jadonk/beagleconnect/hw/Freedom_C4/report.txt

Plot file "C:\Users\Dwin\Desktop\0713\4\BeagleConnect Freedom-F_Cu.dxf" created.
Plot file "C:\Users\Dwin\Desktop\0713\4\BeagleConnect Freedom-GND.dxf" created.
Plot file "C:\Users\Dwin\Desktop\0713\4\BeagleConnect Freedom-PWR.dxf" created.
Plot file "C:\Users\Dwin\Desktop\0713\4\BeagleConnect Freedom-B_Cu.dxf" created.
Plot file "C:\Users\Dwin\Desktop\0713\4\BeagleConnect Freedom-F_Paste.dxf" created.
Plot file "C:\Users\Dwin\Desktop\0713\4\BeagleConnect Freedom-B_Paste.dxf" created.
Plot file "C:\Users\Dwin\Desktop\0713\4\BeagleConnect Freedom-F_SilkS.dxf" created.
Plot file "C:\Users\Dwin\Desktop\0713\4\BeagleConnect Freedom-B_SilkS.dxf" created.
Plot file "C:\Users\Dwin\Desktop\0713\4\BeagleConnect Freedom-F_Mask.dxf" created.
Plot file "C:\Users\Dwin\Desktop\0713\4\BeagleConnect Freedom-B_Mask.dxf" created.
Plot file "C:\Users\Dwin\Desktop\0713\4\BeagleConnect Freedom-Edge_Cuts.dxf" created.
Plot file "C:\Users\Dwin\Desktop\0713\4\BeagleConnect Freedom-F_Fab.dxf" created.
Plot file "C:\Users\Dwin\Desktop\0713\5\BeagleConnect Freedom-F_Cu.gtl" created.
Plot file "C:\Users\Dwin\Desktop\0713\5\BeagleConnect Freedom-GND.g2" created.
Plot file "C:\Users\Dwin\Desktop\0713\5\BeagleConnect Freedom-PWR.g3" created.
Plot file "C:\Users\Dwin\Desktop\0713\5\BeagleConnect Freedom-B_Cu.gbl" created.
Plot file "C:\Users\Dwin\Desktop\0713\5\BeagleConnect Freedom-F_Paste.gtp" created.
Plot file "C:\Users\Dwin\Desktop\0713\5\BeagleConnect Freedom-B_Paste.gbp" created.
Plot file "C:\Users\Dwin\Desktop\0713\5\BeagleConnect Freedom-F_SilkS.gto" created.
Plot file "C:\Users\Dwin\Desktop\0713\5\BeagleConnect Freedom-B_SilkS.gbo" created.
Plot file "C:\Users\Dwin\Desktop\0713\5\BeagleConnect Freedom-F_Mask.gts" created.
Plot file "C:\Users\Dwin\Desktop\0713\5\BeagleConnect Freedom-B_Mask.gbs" created.
Plot file "C:\Users\Dwin\Desktop\0713\5\BeagleConnect Freedom-Edge_Cuts.gm1" created.
创建 Gerber 工作文件 C:\Users\Dwin\Desktop\0713\5\BeagleConnect Freedom-job.gbrjob
