jadonk/beagleconnect/case/Industrial design/base-pcb1.png

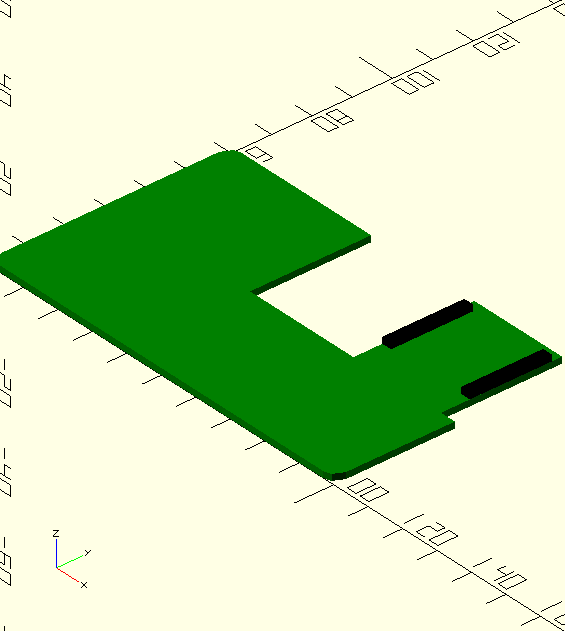
case/Industrial design/base-pcb1.png
