jadonk/beagleconnect/case/Industrial design/BeagleConnect_ID_4.png

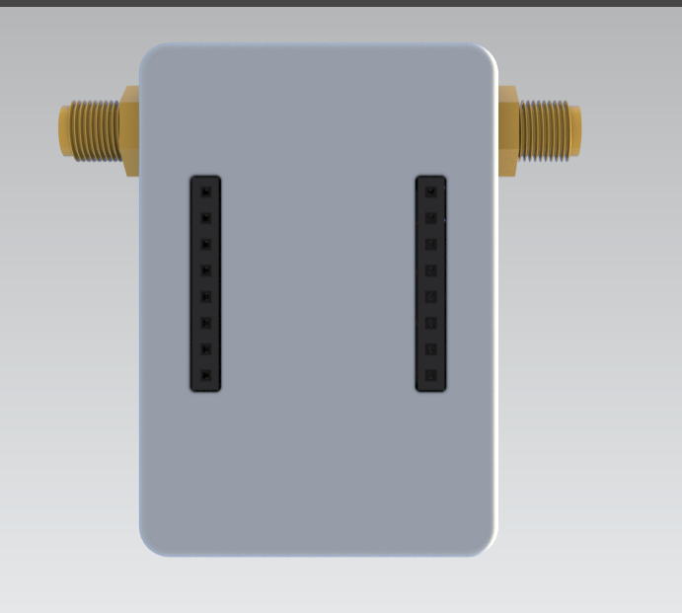
case/Industrial design/BeagleConnect_ID_4.png
