jadonk/beagleconnect/case/Industrial design/BeagleConnect_ID_5.png

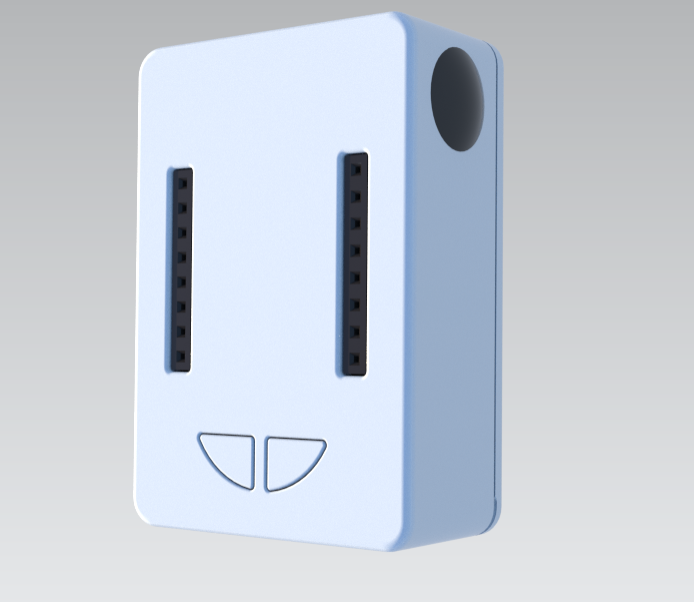
case/Industrial design/BeagleConnect_ID_5.png
