jadonk/beagleconnect/case/Industrial design/BeagleConnect_ID_6.png

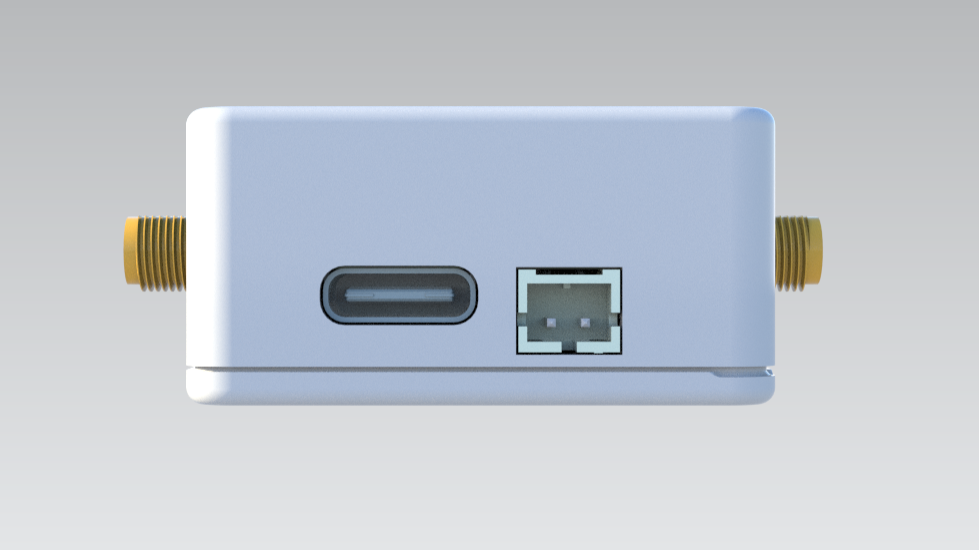
case/Industrial design/BeagleConnect_ID_6.png
