jadonk/beagleconnect/case/Industrial design/BeagleConnnect_ID_8.png

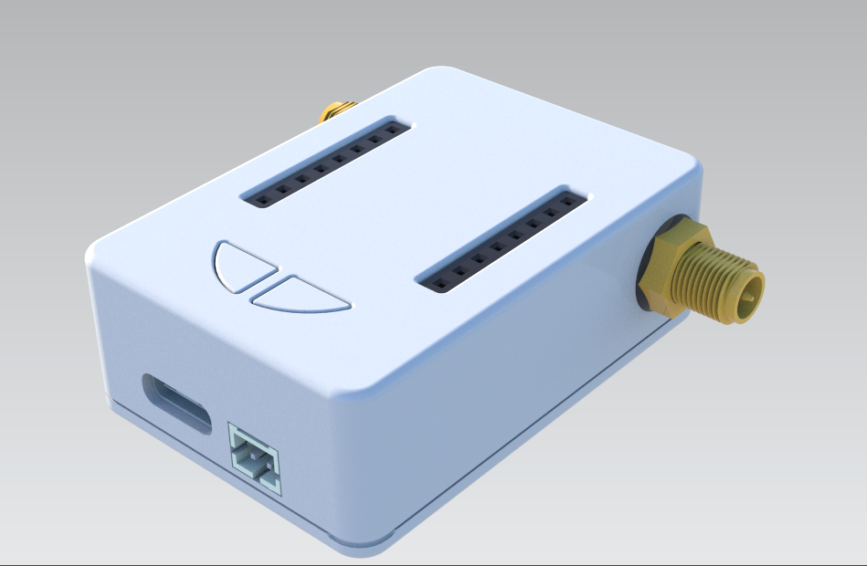
case/Industrial design/BeagleConnnect_ID_8.png
