jadonk/beagleconnect/case/Industrial design/ID-20210603-jk.png

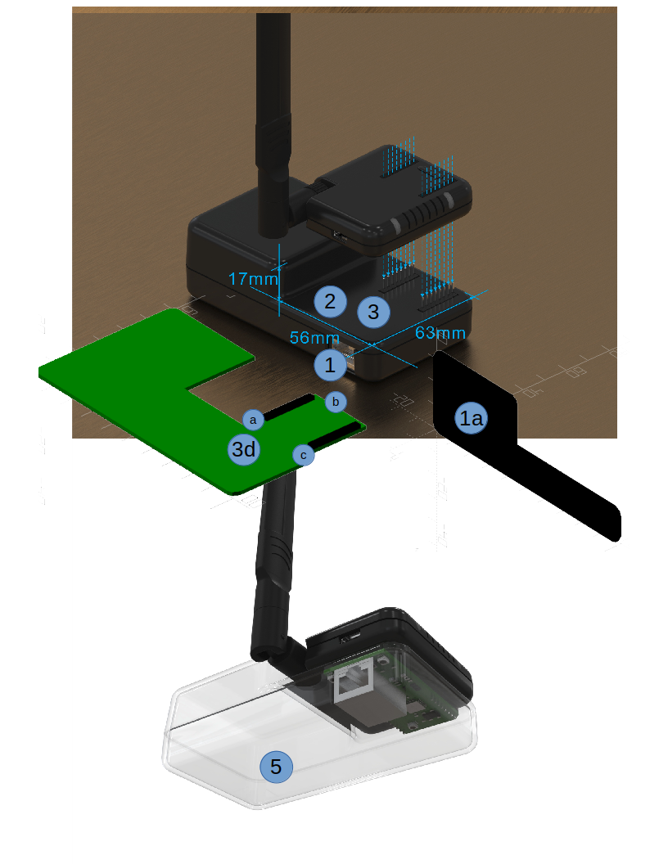
case/Industrial design/ID-20210603-jk.png
