jadonk/beagleconnect/case/mechanical design/case-silkscreen.png

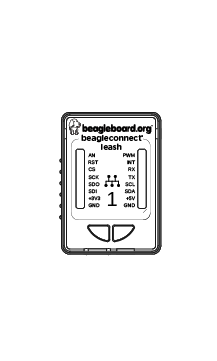
case/mechanical design/case-silkscreen.png
