jadonk/beagleconnect/docs/MVIMG_20200410_095337.jpg

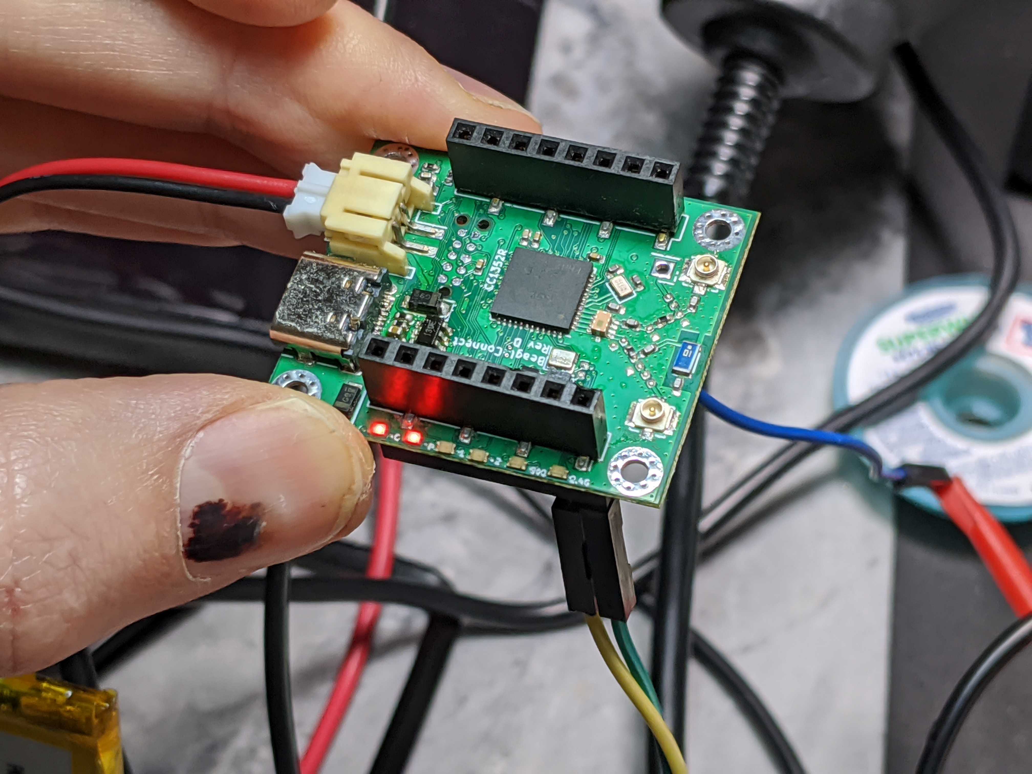
docs/MVIMG_20200410_095337.jpg
