jadonk/beagleconnect/docs/SoftwareProp.PNG

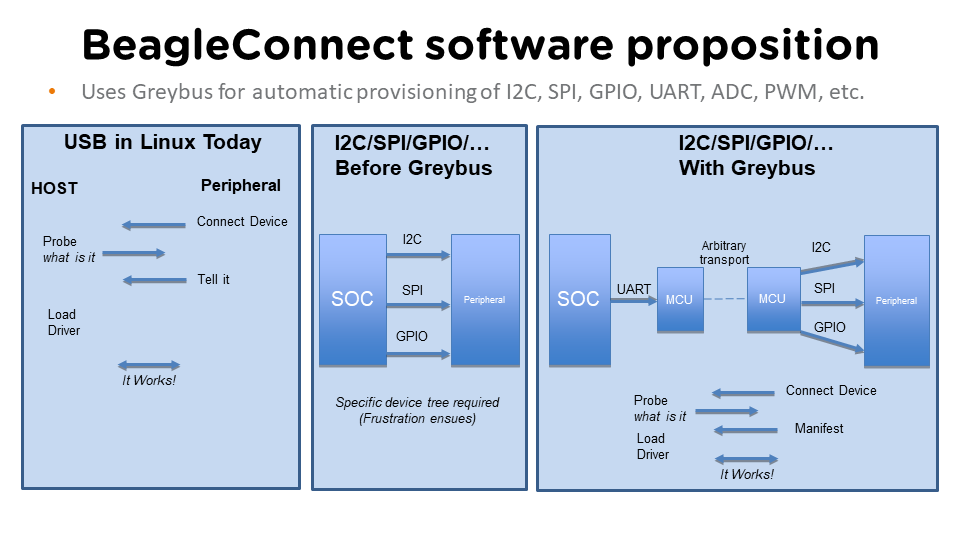
docs/SoftwareProp.PNG
