jadonk/beagleconnect/graphics/bb-code-server-closeup.png

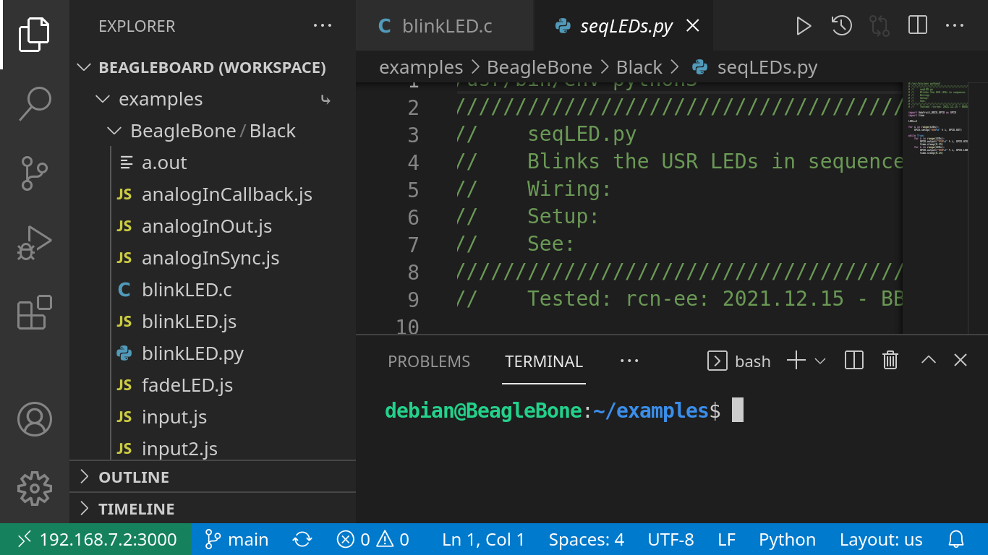
graphics/bb-code-server-closeup.png
