jadonk/beagleconnect/graphics/bb-code-server.png

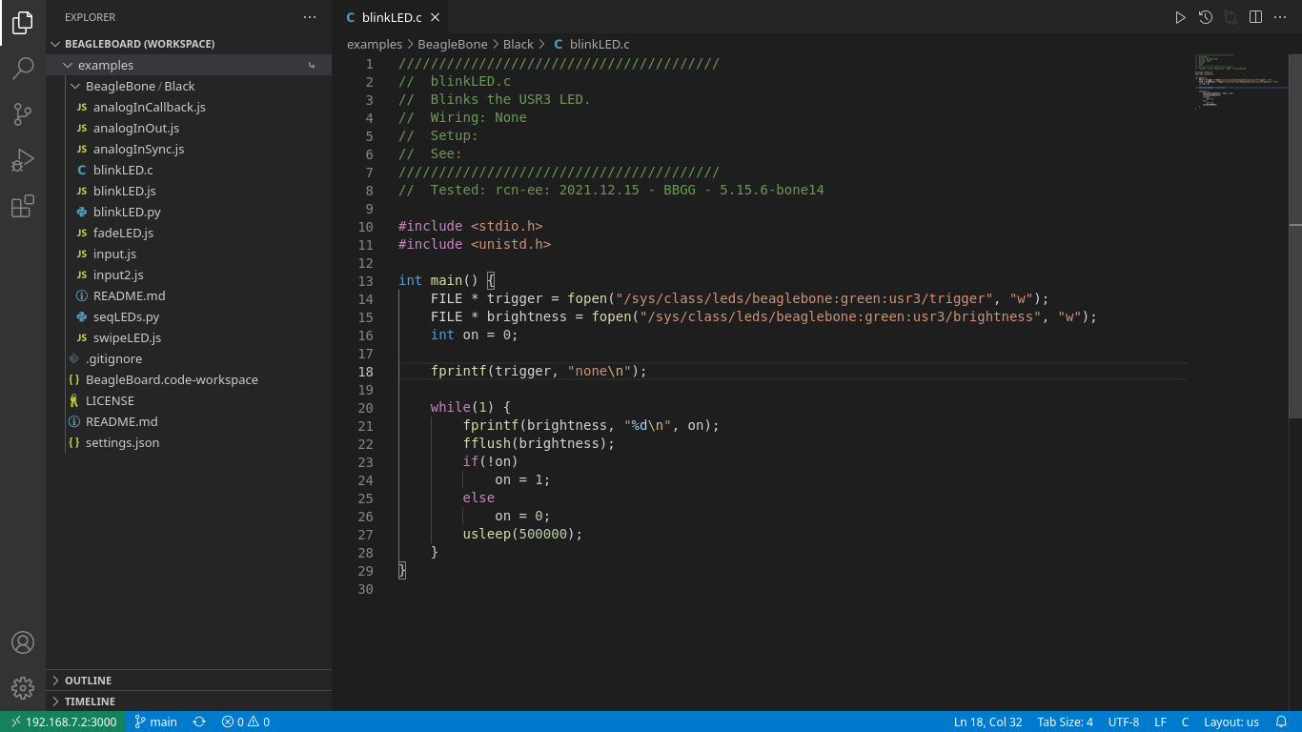
graphics/bb-code-server.png
