jadonk/beagleconnect/graphics/BeagleConnect-Freedom-C5-Boards-Presentation.png

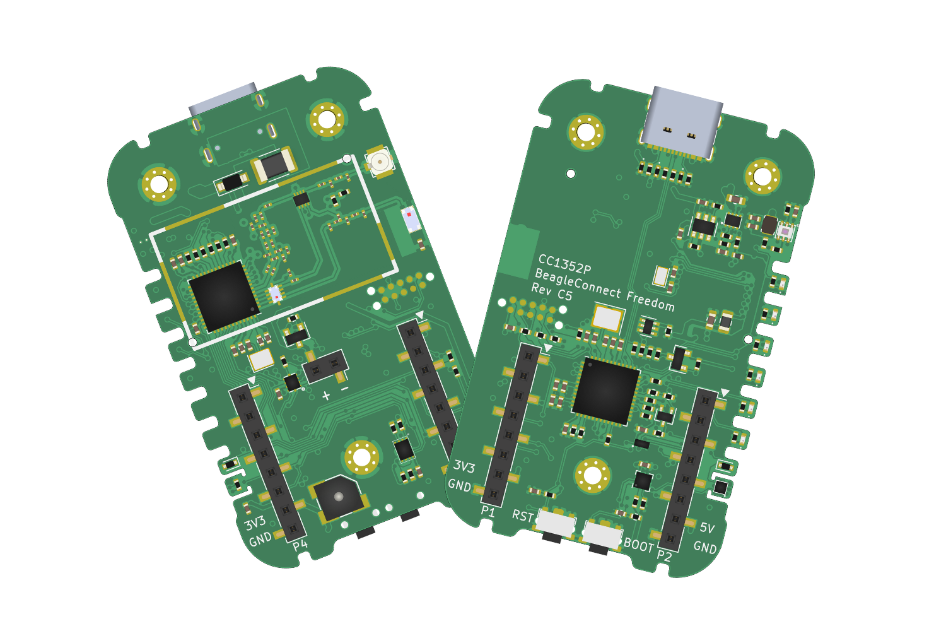
graphics/BeagleConnect-Freedom-C5-Boards-Presentation.png
