jadonk/beagleconnect/graphics/BeagleConnectFreedom-Back-Annotated.png

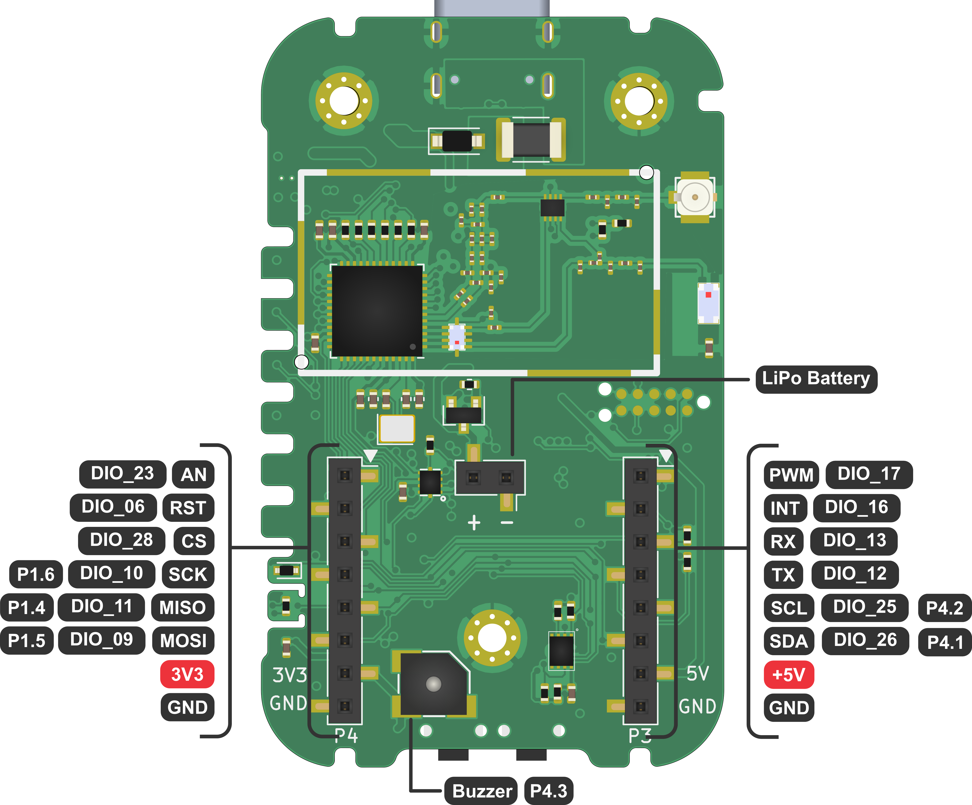
graphics/BeagleConnectFreedom-Back-Annotated.png
