jadonk/beagleconnect/graphics/BeagleConnectFreedom-Back.png

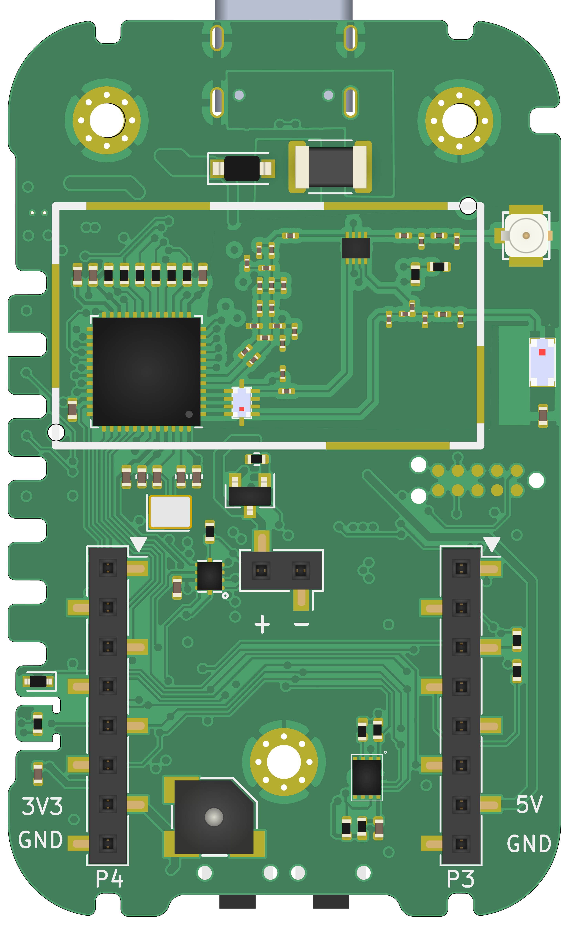
graphics/BeagleConnectFreedom-Back.png
