jadonk/beagleconnect/graphics/BeagleConnectFreedom-Front-Annotated.png

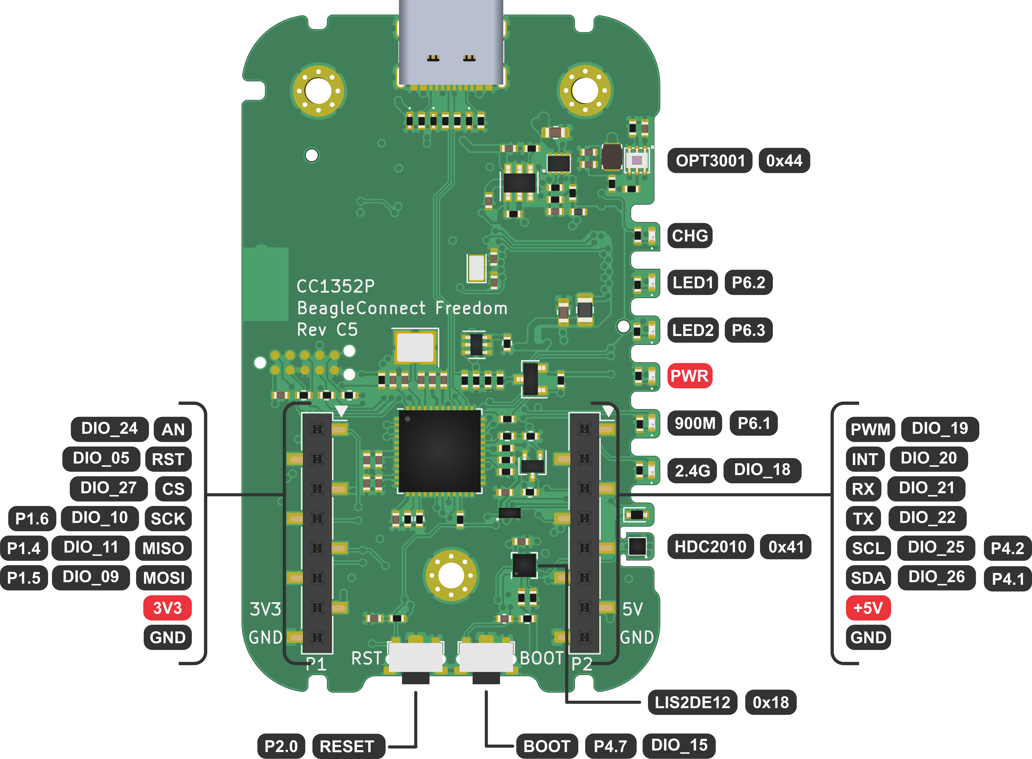
graphics/BeagleConnectFreedom-Front-Annotated.png
