jadonk/beagleconnect/graphics/BeagleConnectFreedom-Front.png

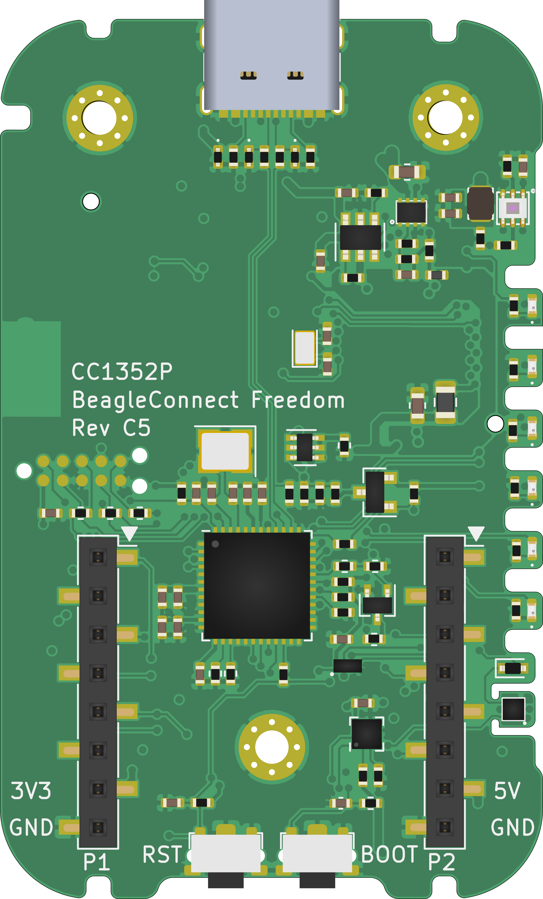
graphics/BeagleConnectFreedom-Front.png
