jadonk/beagleconnect/hw/Freedom_C4/mech/YPA0006ABAB_TEX.step

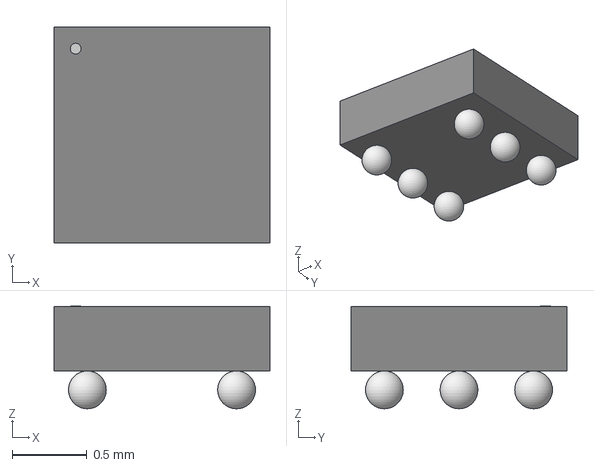
[picture p70: CAD file, 2020-08-28]
hw/Freedom_C4/mech/YPA0006ABAB_TEX.step
1.45 x 1.45 x 0.688 mm
