jadonk/beagleconnect/hw/Freedom_C4/mech/LGA-12_STM-M.step

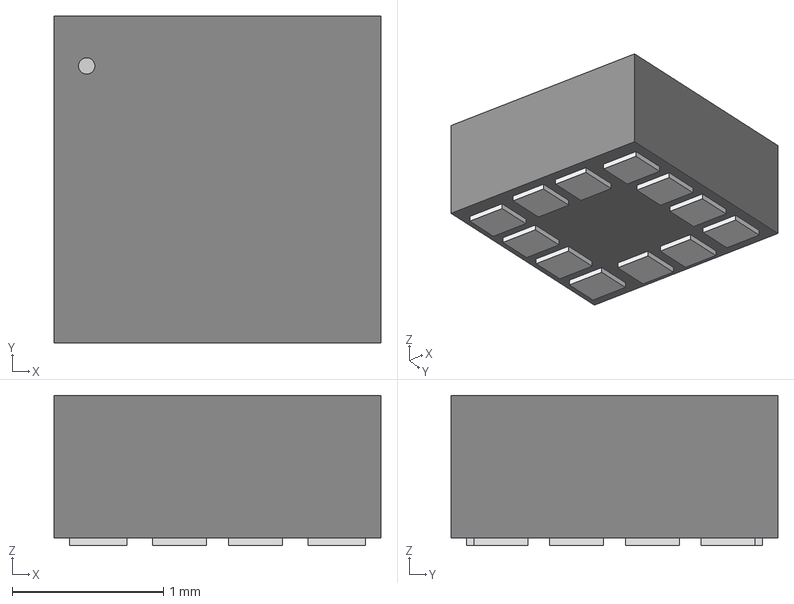
[picture p71: CAD file, 2020-08-28]
hw/Freedom_C4/mech/LGA-12_STM-M.step
2.16 x 2.16 x 0.993 mm
