jadonk/beagleconnect/hw/Freedom_C4/mech/USB Type C Port (SMD Type).STEP

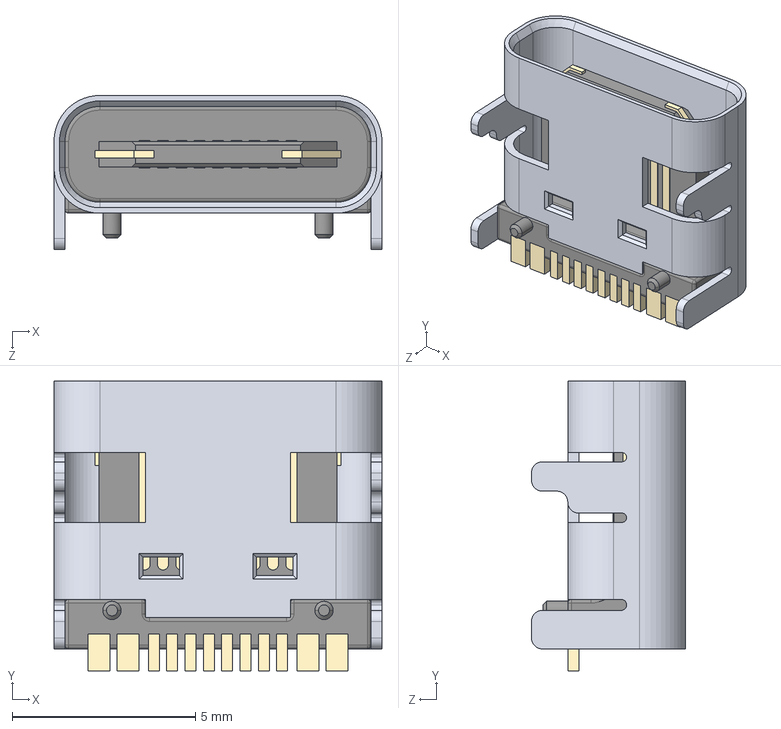
[picture p72: CAD file, 2020-08-28]
hw/Freedom_C4/mech/USB Type C Port (SMD Type).STEP
8.94 x 7.90 x 4.20 mm
