jadonk/beagleconnect/hw/Freedom_C4/mech/a_1jb_3d_model_file.stp

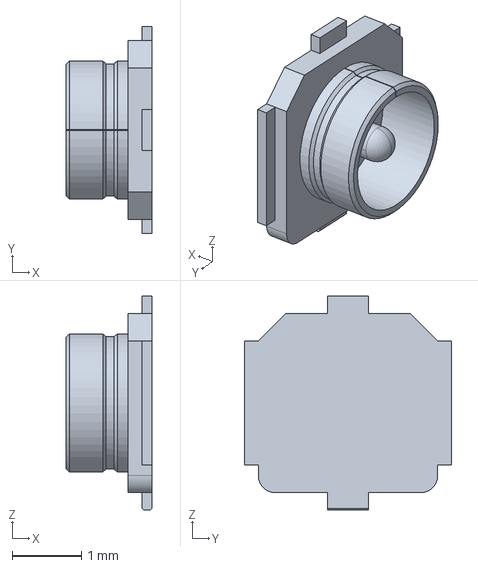
[picture p73: CAD file, 2019-07-19]
hw/Freedom_C4/mech/a_1jb_3d_model_file.stp
1.25 x 3.00 x 3.10 mm
