jadonk/beagleconnect/hw/Freedom_C4/mech/EVQP7-JA-01P.STEP

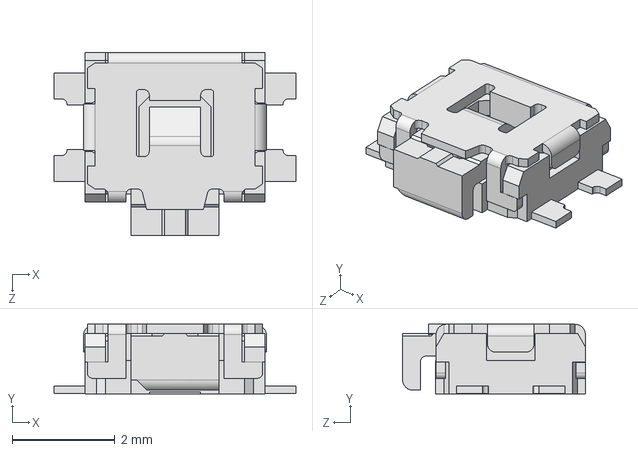
[picture p74: CAD file, 2019-07-19]
hw/Freedom_C4/mech/EVQP7-JA-01P.STEP
4.70 x 1.35 x 3.55 mm
