jadonk/beagleconnect/hw/Freedom_C4/mech/AAA Battery.STEP

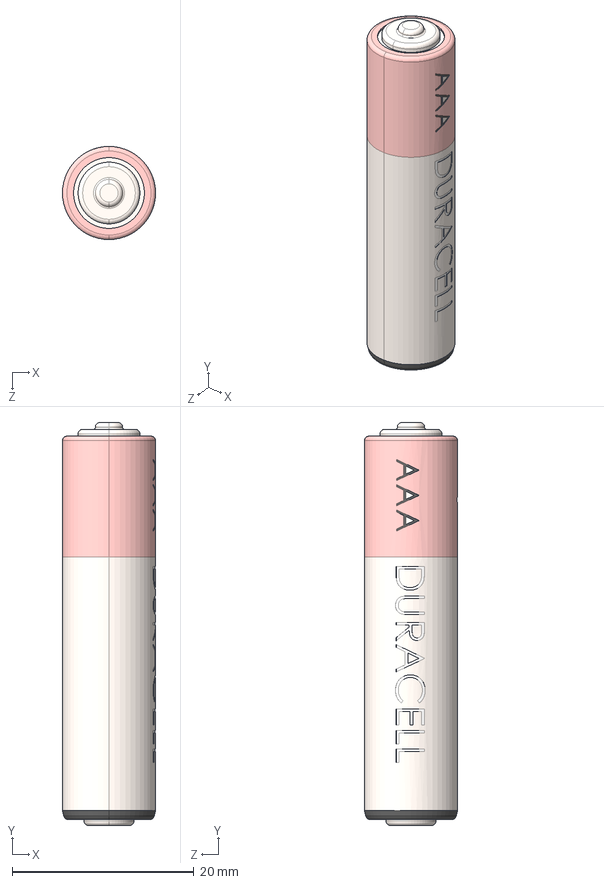
[picture p75: CAD file, 2019-07-19]
hw/Freedom_C4/mech/AAA Battery.STEP
10.2 x 44.4 x 10.2 mm
