jadonk/beagleconnect/hw/Freedom_C4/mech/Leash_061319.step

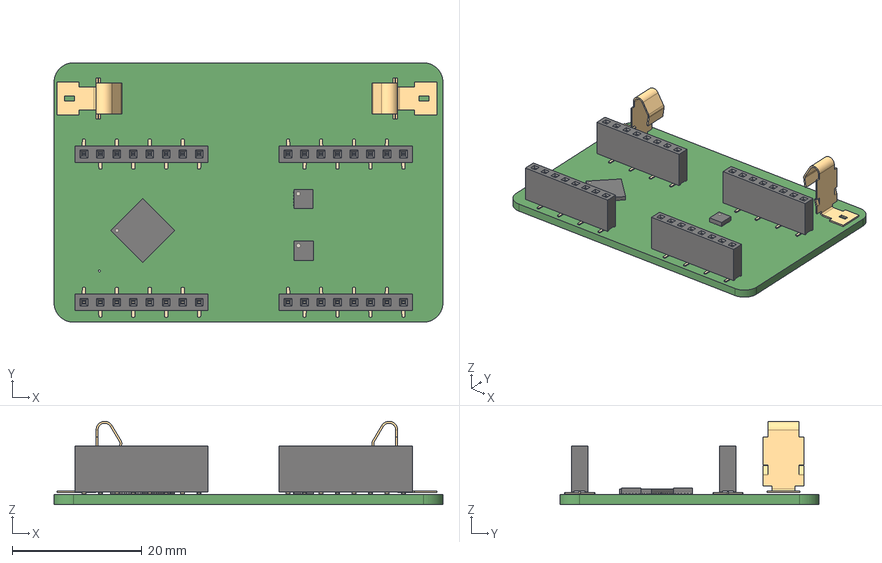
[picture p76: CAD file, 2019-06-13]
hw/Freedom_C4/mech/Leash_061319.step
60.0 x 40.0 x 12.9 mm
