jadonk/beagleconnect/docs/ProvStep1.PNG

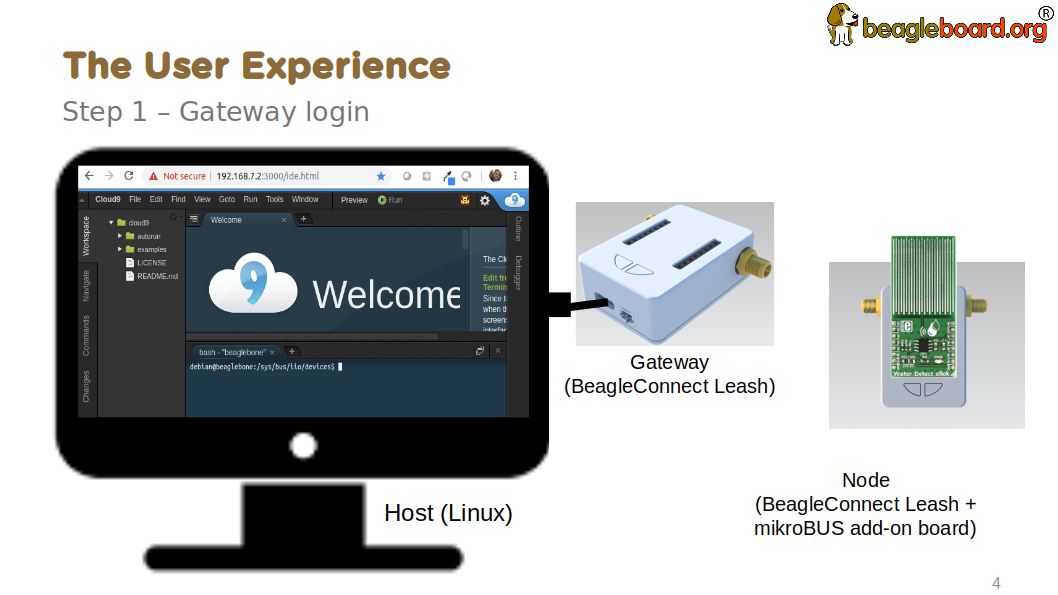
docs/ProvStep1.PNG
