jadonk/beagleconnect/hw/Leash/BeagleConnect.pdf

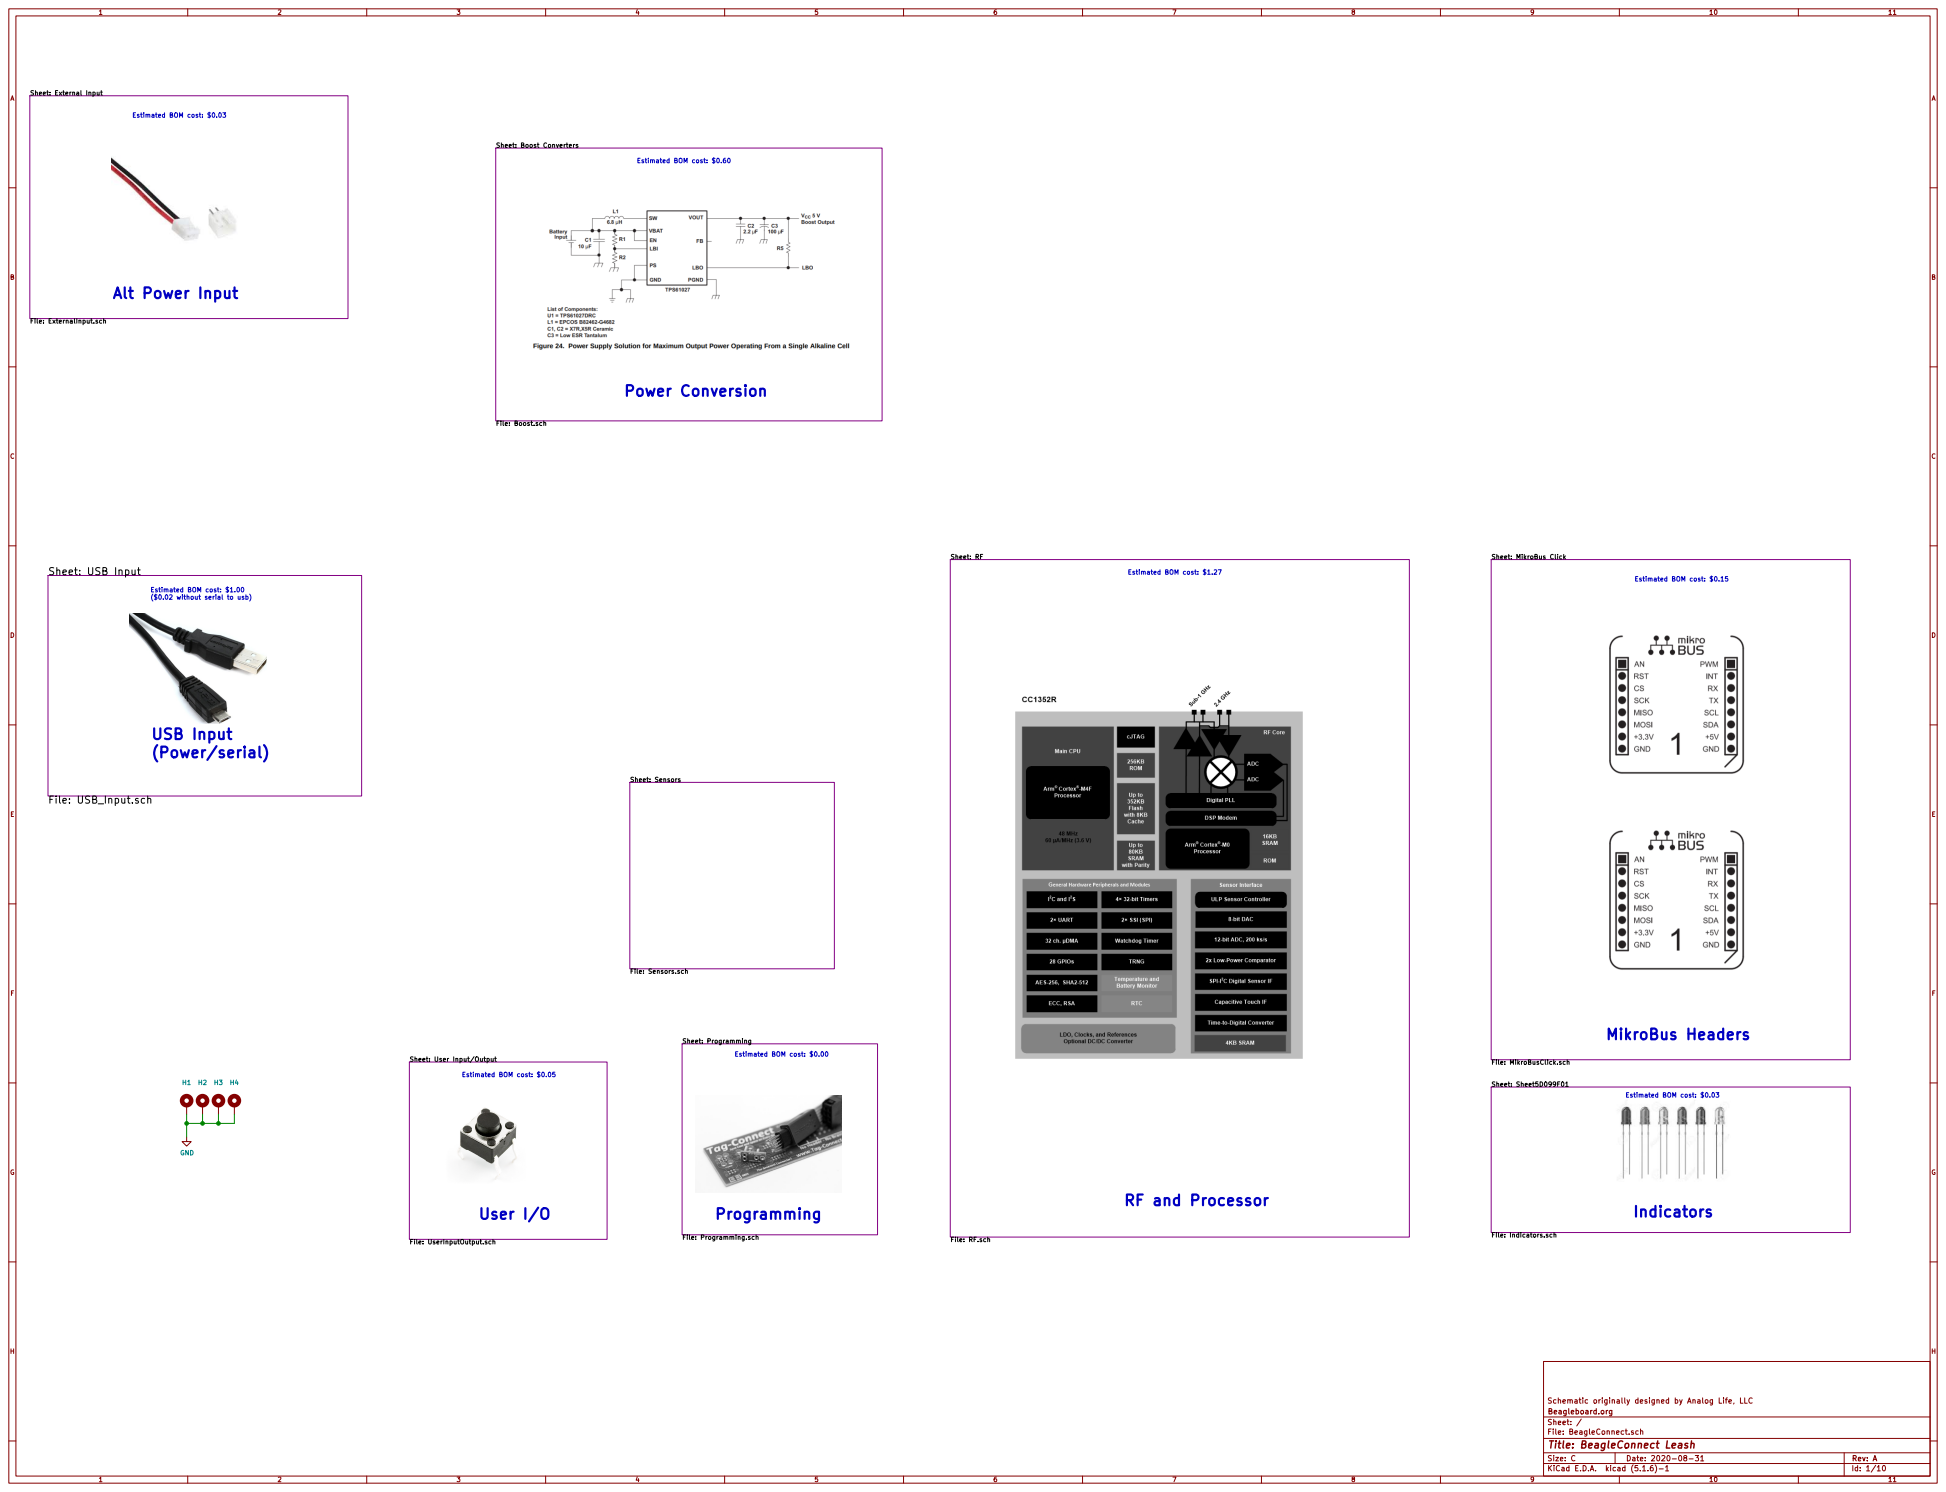
[picture p92: page 1]

Sheet: Boost Converters File: Boost.sch Sheet: USB Input

Estimated BOM cost: $1.00
($0.02 without serial to usb)

Sheet: Sensors File: Sensors.sch Sheet: User Input/Output

Sheet: Sheet5D099F01 File: Indicators.sch GND

Schematic originally designed by Analog Life, LLC
File: BeagleConnect.sch Sheet: / Beagleboard.org

Id: 1/10 Title: BeagleConnect Leash

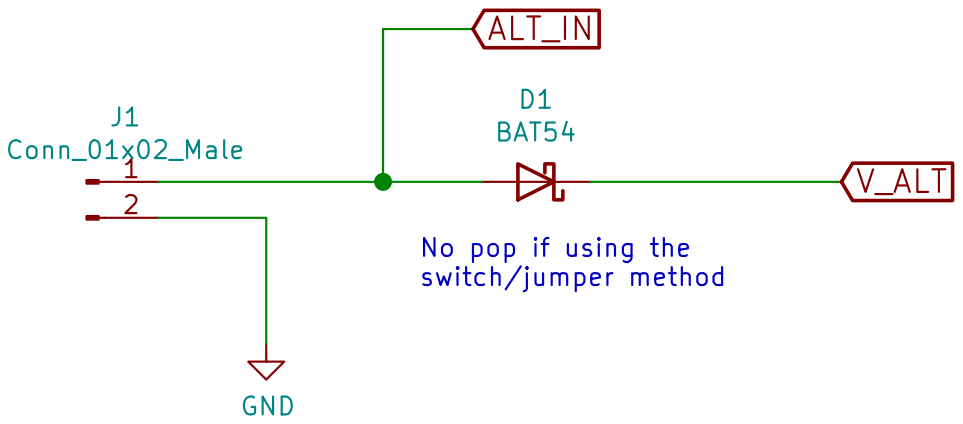
[picture p93: page 2]

No pop if using the
switch/jumper method

Schematic originally designed by Analog Life, LLC
Beagleboard.org
Sheet: /External Input/
File: ExternalInput.sch
Id: 2/10 Title: BeagleConnect Leash

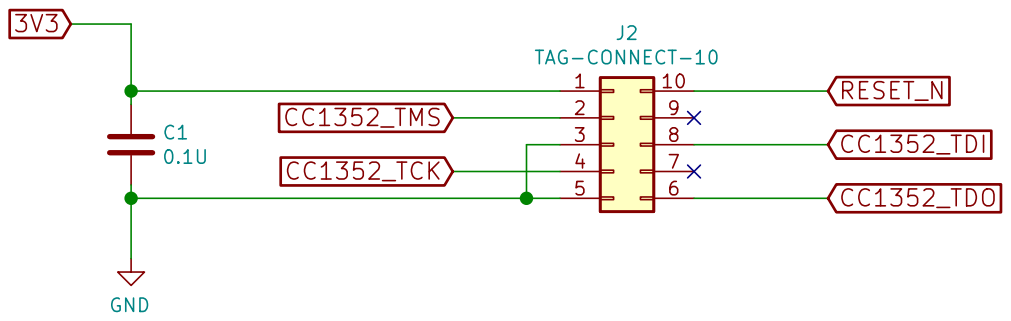
[picture p94: page 3]

Schematic originally designed by Analog Life, LLC
Beagleboard.org
Sheet: /Programming/
File: Programming.sch
Id: 3/10 Title: BeagleConnect Leash


Schematic originally designed by Analog Life, LLC
File: Indicators.sch Sheet: /Sheet5D099F01/ Beagleboard.org

Id: 4/10 Title: BeagleConnect Leash

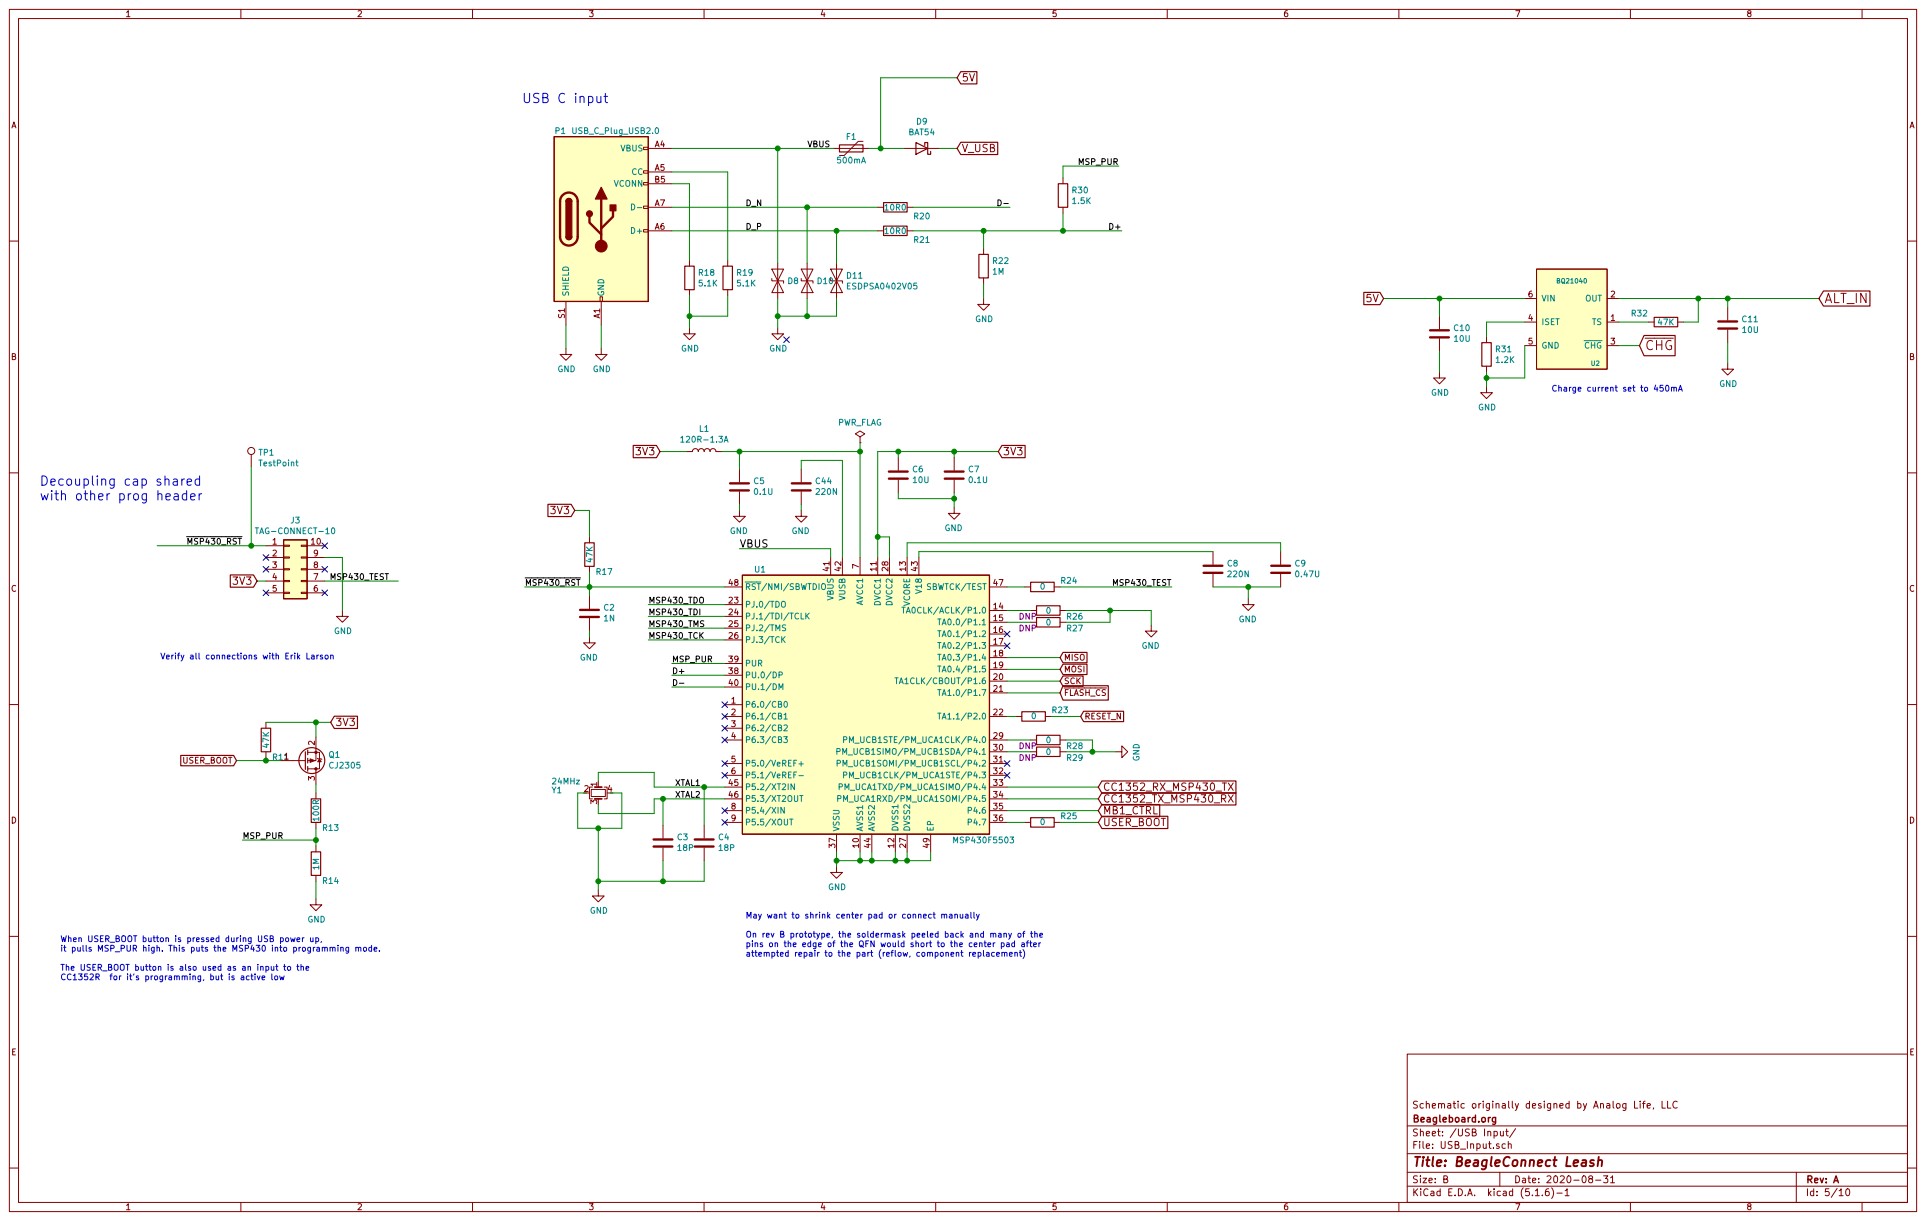
[picture p95: page 5]

Charge current set to 450mA

Decoupling cap shared
with other prog header

Verify all connections with Erik Larson

When USER_BOOT button is pressed during USB power up,
it pulls MSP_PUR high. This puts the MSP430 into programming mode.

On rev B prototype, the soldermask peeled back and many of the
pins on the edge of the QFN would short to the center pad after
attempted repair to the part (reflow, component replacement)

The USER_BOOT button is also used as an input to the
CC1352R for it's programming, but is active low

Schematic originally designed by Analog Life, LLC
Beagleboard.org
Sheet: /USB Input/
File: USB_Input.sch
Id: 5/10 Title: BeagleConnect Leash

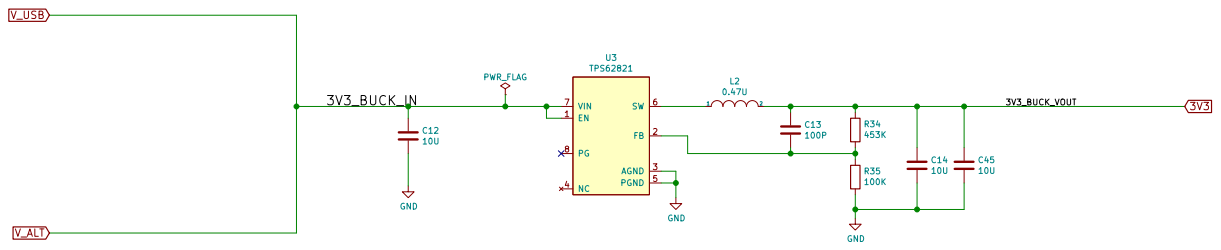
[picture p96: page 6]

Schematic originally designed by Analog Life, LLC
File: Boost.sch Sheet: /Boost Converters/ Beagleboard.org

Id: 6/10 Title: BeagleConnect Leash


Schematic originally designed by Analog Life, LLC
File: MikroBusClick.sch Sheet: /MikroBus Click/ Beagleboard.org

Id: 7/10 Title: BeagleConnect Leash

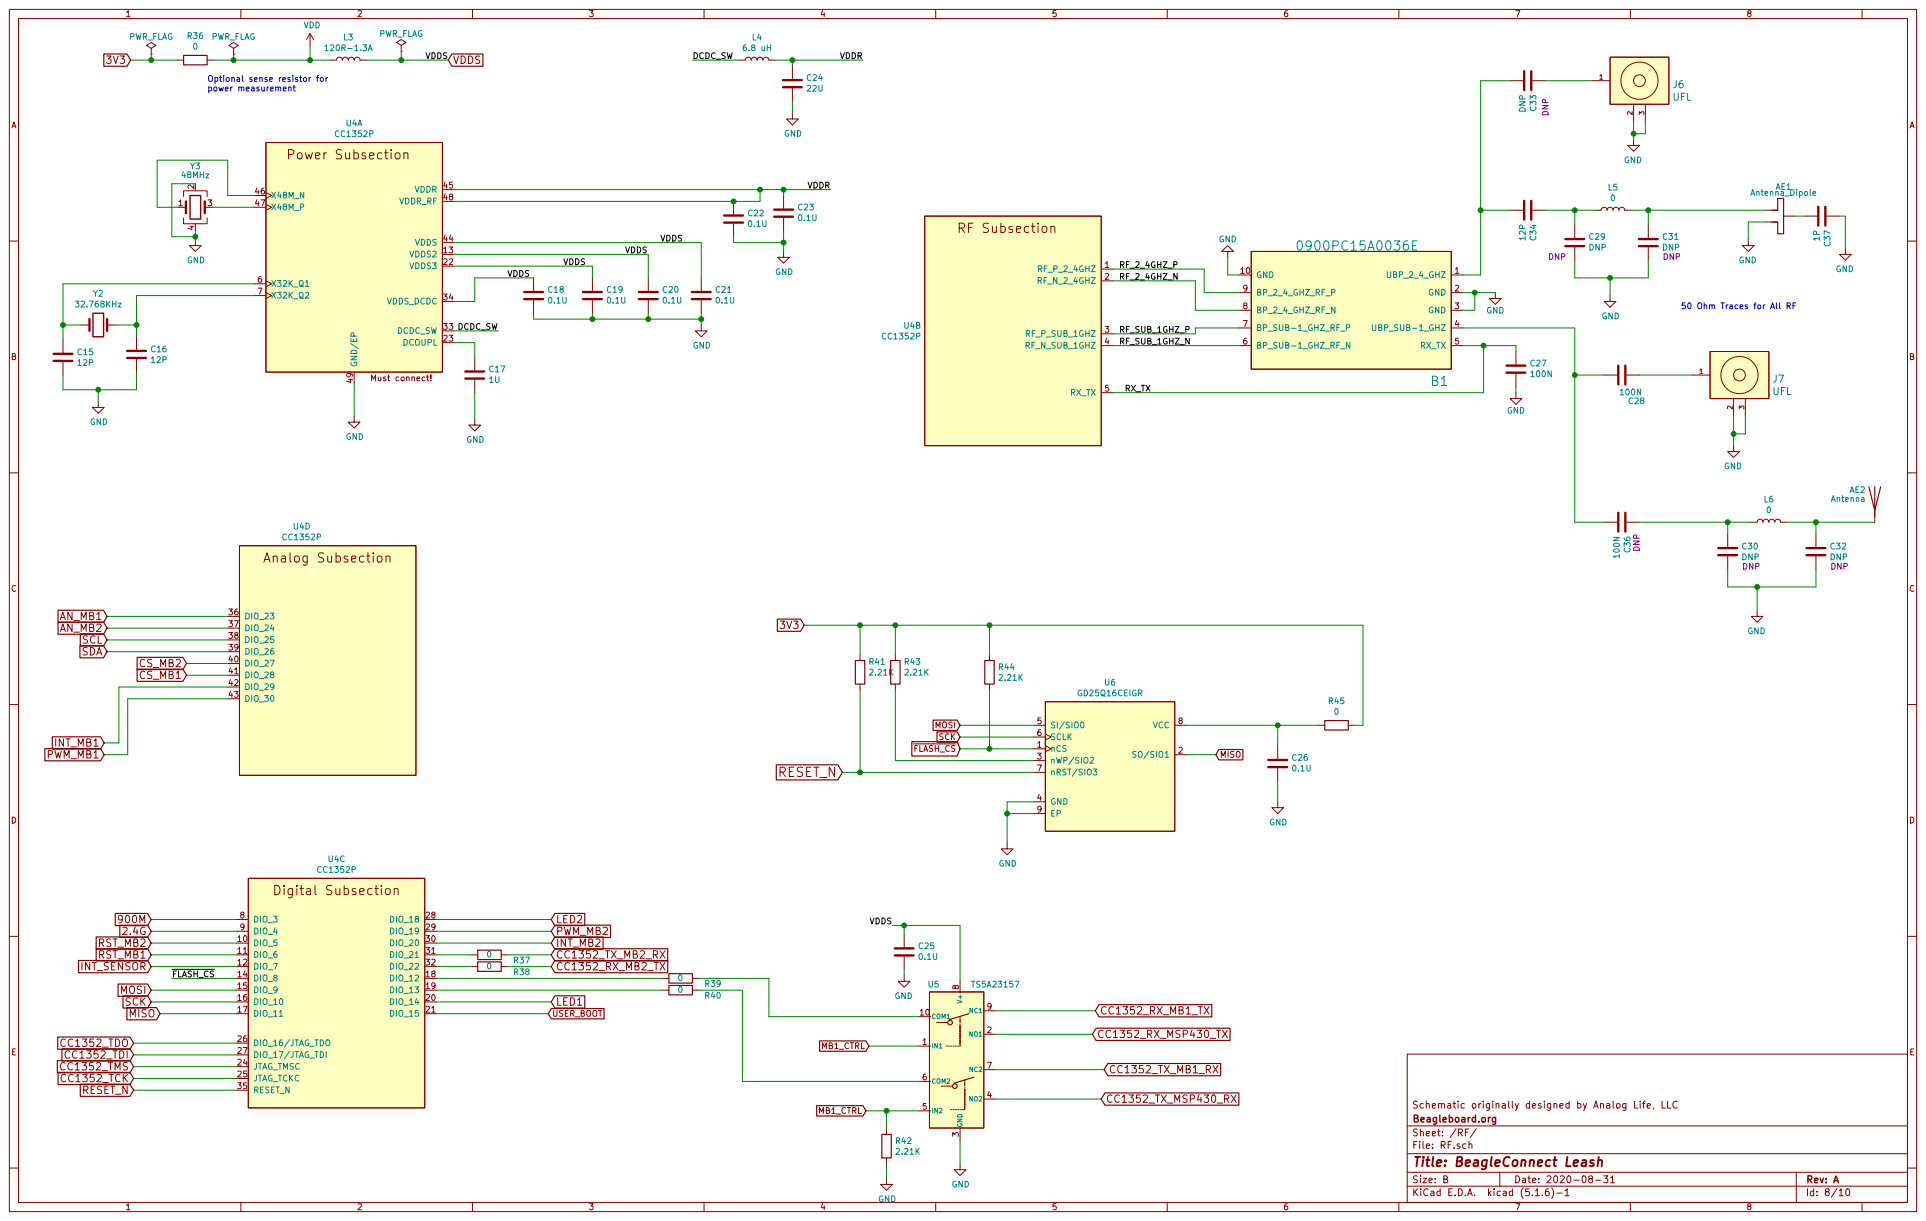
[picture p97: page 8]

50 Ohm Traces for All RF Optional sense resistor for power measurement

Schematic originally designed by Analog Life, LLC
File: RF.sch Sheet: /RF/ Beagleboard.org

Id: 8/10 Title: BeagleConnect Leash

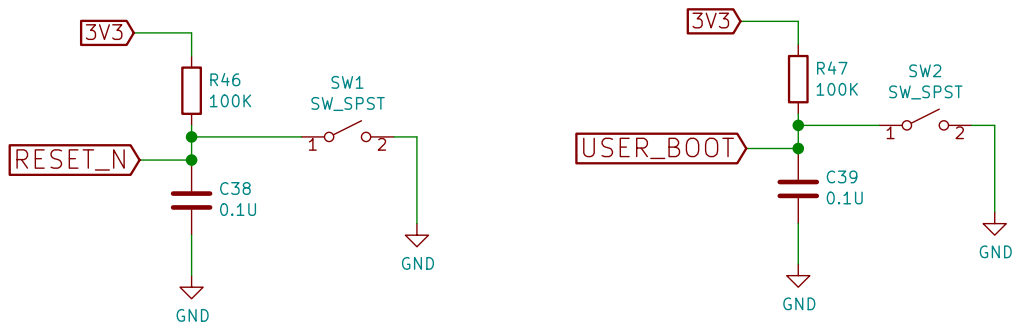
[picture p98: page 9]

Schematic originally designed by Analog Life, LLC
Beagleboard.org
Sheet: /User Input/Output/
File: UserInputOutput.sch
Id: 9/10 Title: BeagleConnect Leash

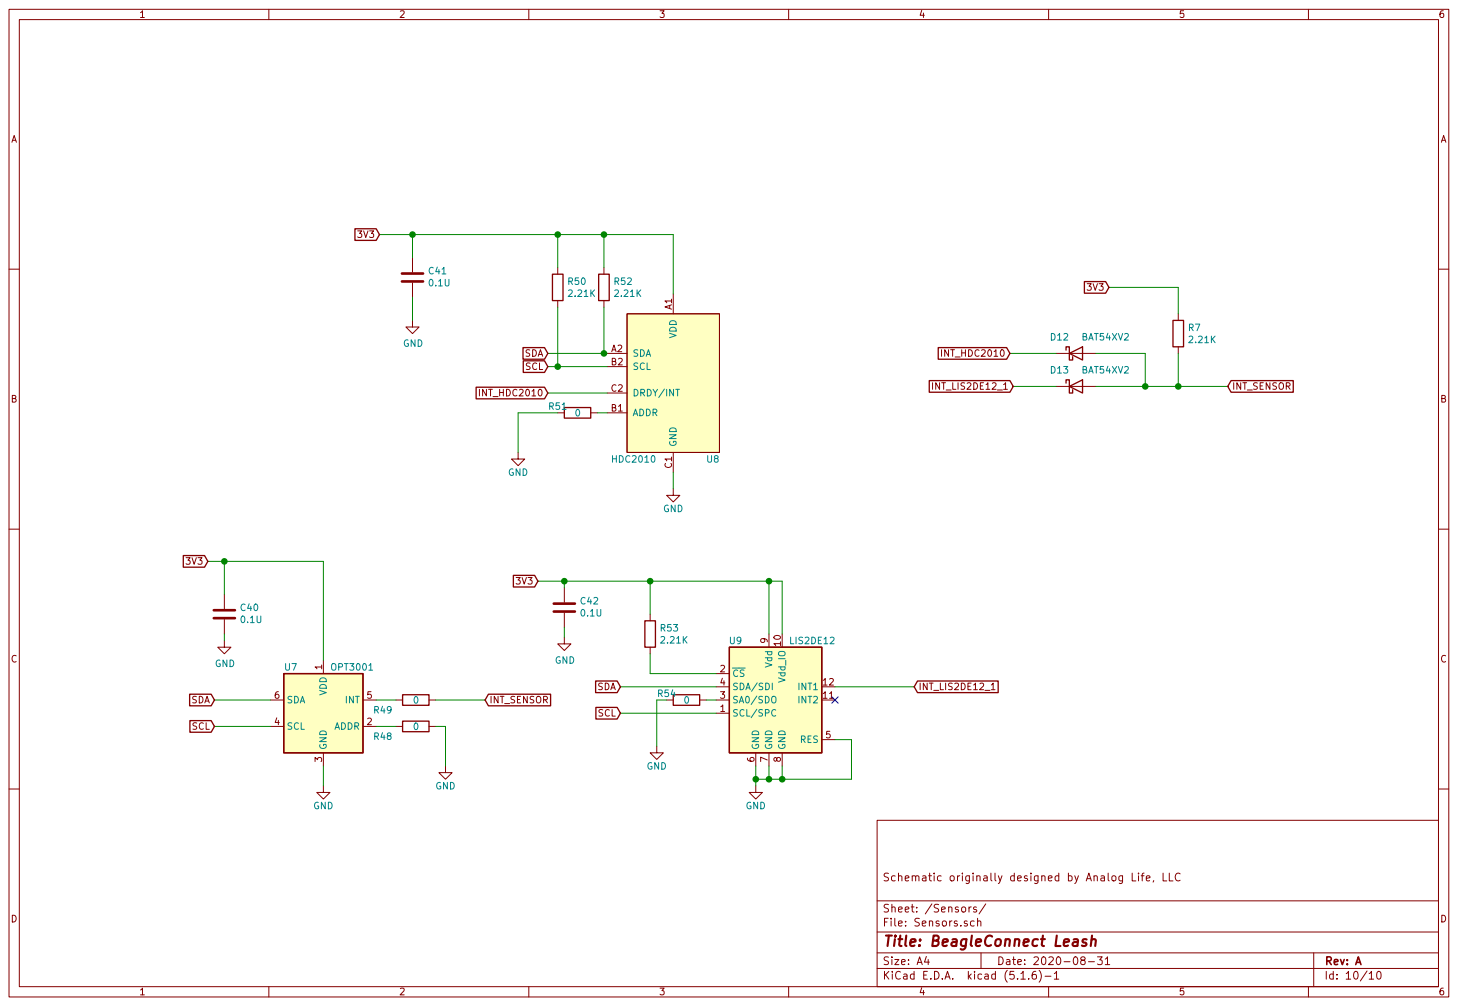
[picture p99: page 10]

File: Sensors.sch Sheet: /Sensors/ Schematic originally designed by Analog Life, LLC

Id: 10/10 Title: BeagleConnect Leash
