jadonk/beagleconnect/hw/Freedom_C4/gerber/0722.pdf

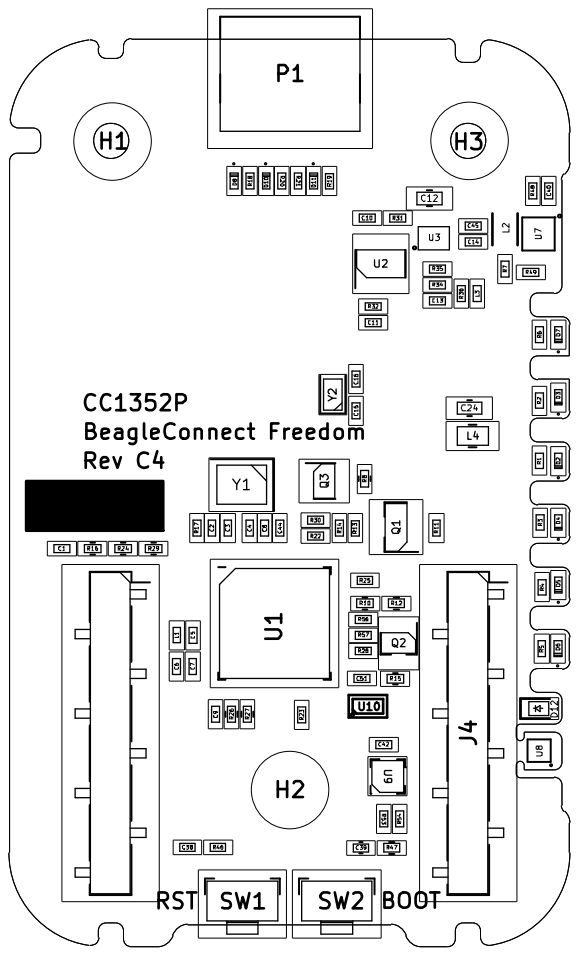
[picture p117: page 1]
