jadonk/beagleconnect/hw/Freedom_C4/mech/TopLayerAntenna.pdf

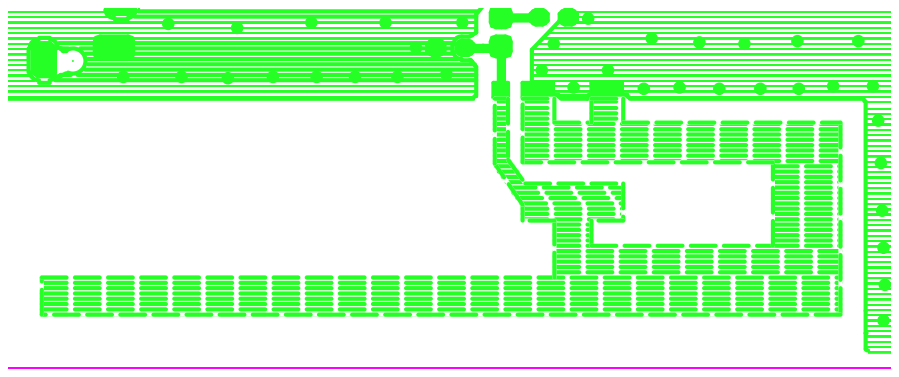
[picture p118: page 1]
