jadonk/beagleconnect/hw/Freedom/BeagleConnect Freedom.pdf

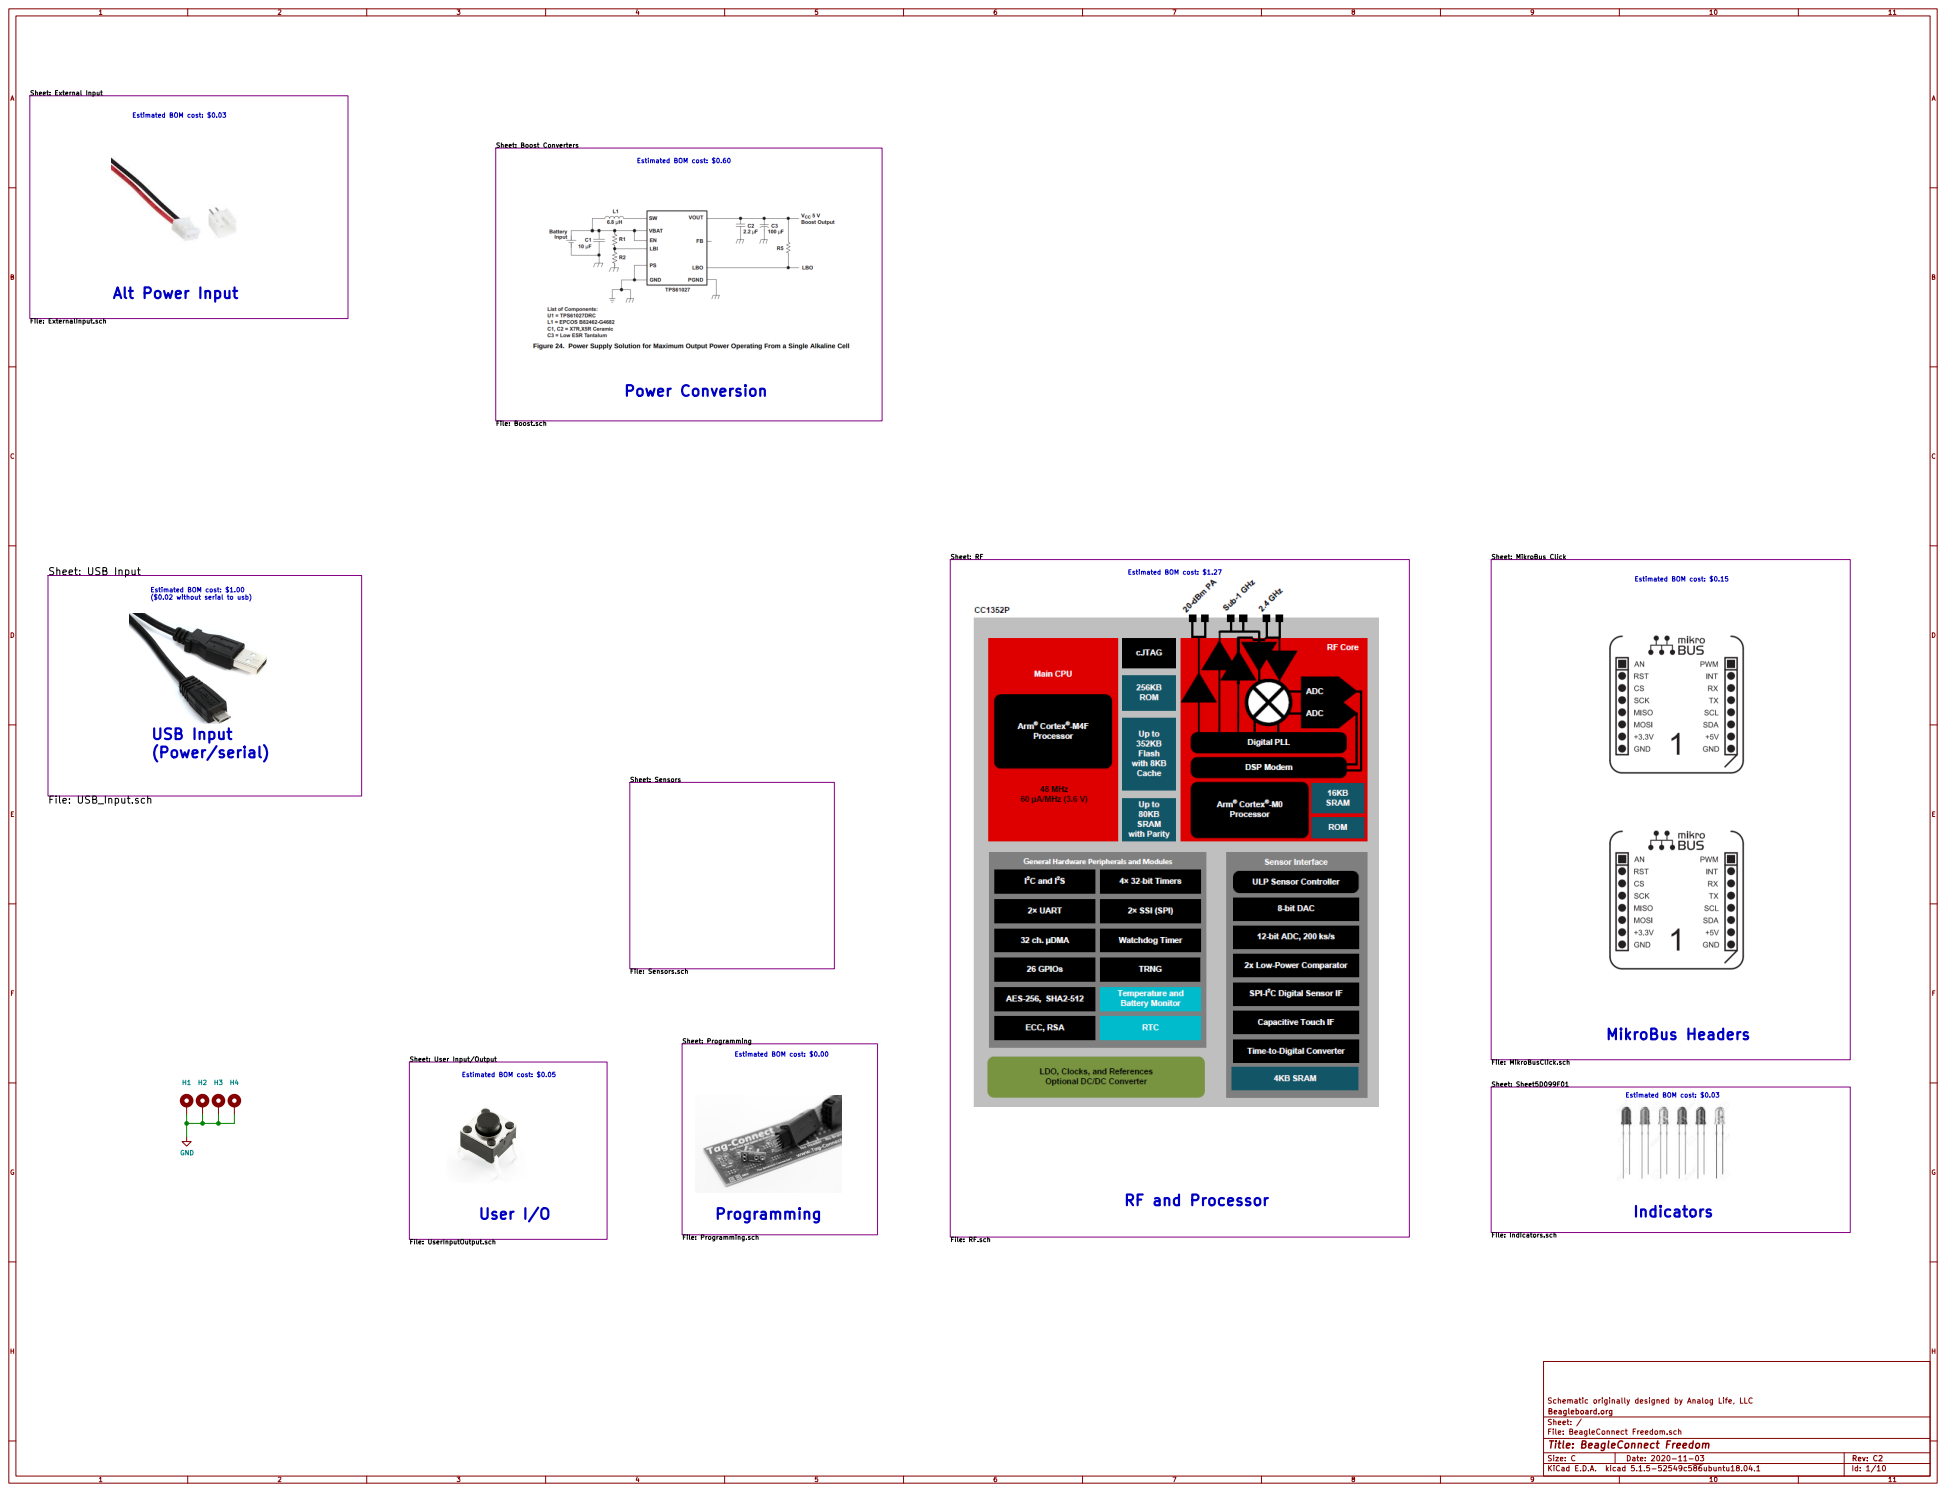
[picture p119: page 1]

Estimated BOM cost: $0.60 Estimated BOM cost: $1.00

Estimated BOM cost: $1.27 USB Input

($0.02 without serial to usb)

Sheet: Sensors File: Sensors.sch Sheet: User Input/Output File: UserInputOutput.sch

Sheet: Programming File: Programming.sch

Sheet: Sheet5D099F01 File: Indicators.sch GND

File: BeagleConnect Freedom.sch Sheet: / Beagleboard.org Schematic originally designed by Analog Life, LLC

Id: 1/10 Title: BeagleConnect Freedom

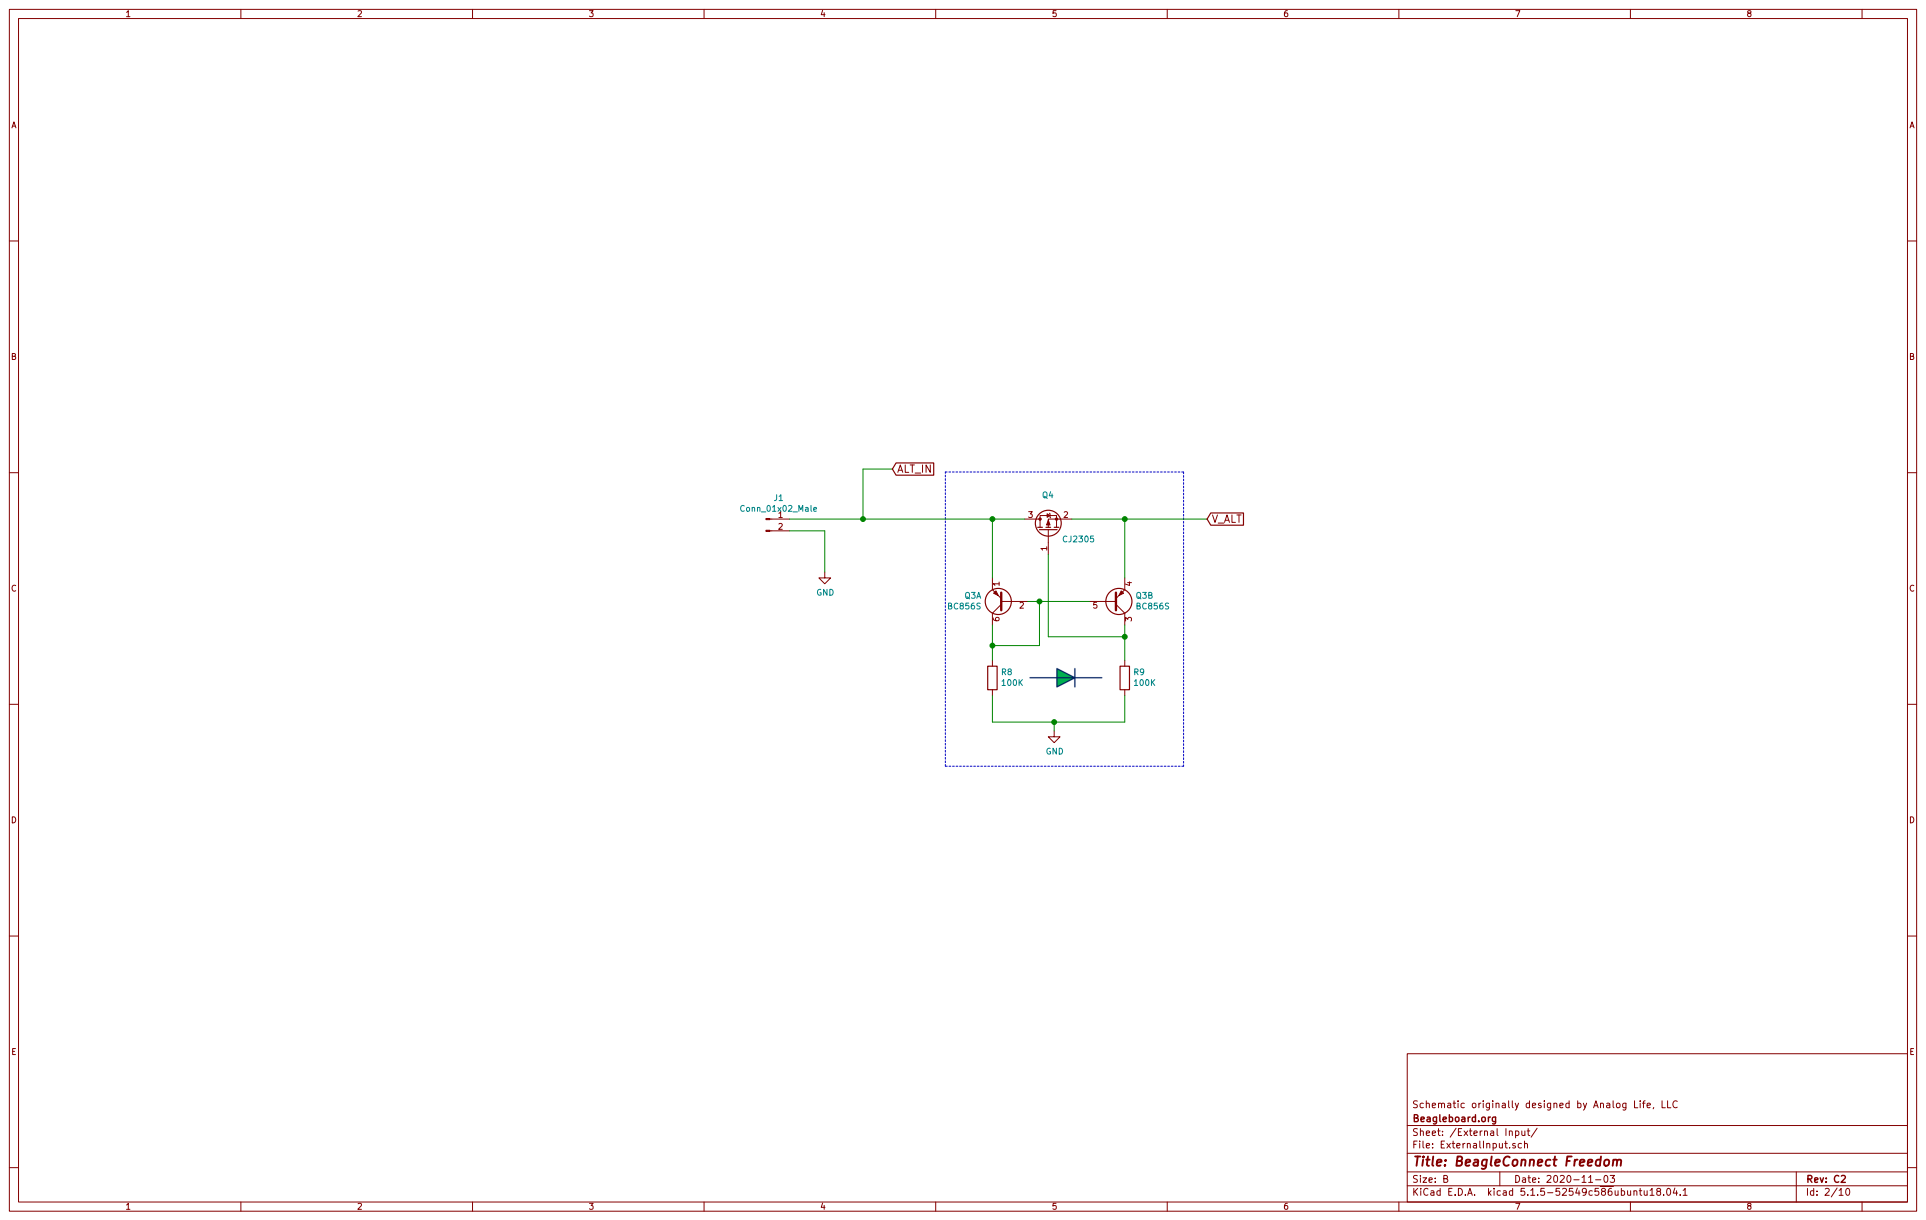
[picture p120: page 2]

File: ExternalInput.sch Sheet: /External Input/ Beagleboard.org Schematic originally designed by Analog Life, LLC

Id: 2/10 Title: BeagleConnect Freedom

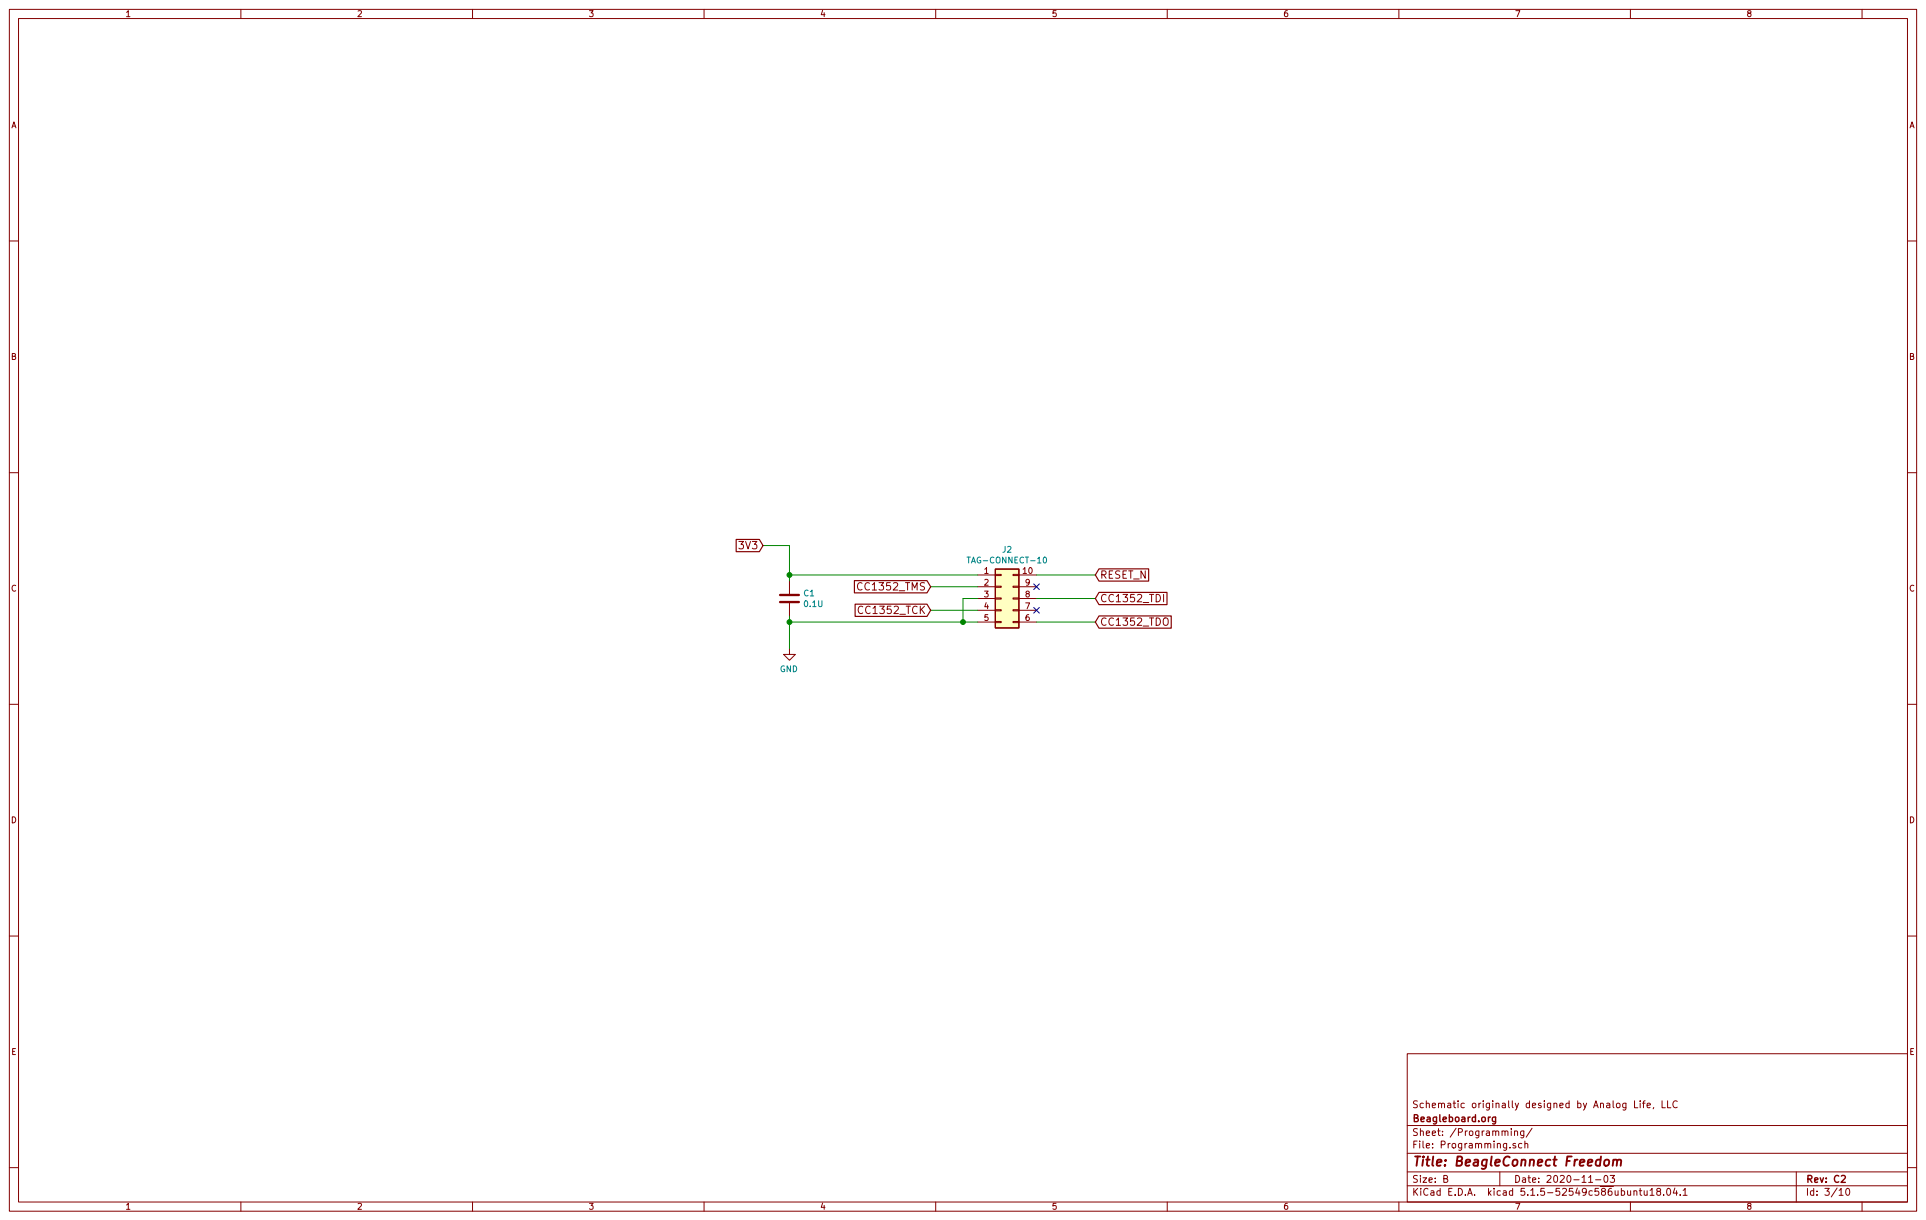
[picture p121: page 3]

File: Programming.sch Sheet: /Programming/ Beagleboard.org Schematic originally designed by Analog Life, LLC

Id: 3/10 Title: BeagleConnect Freedom

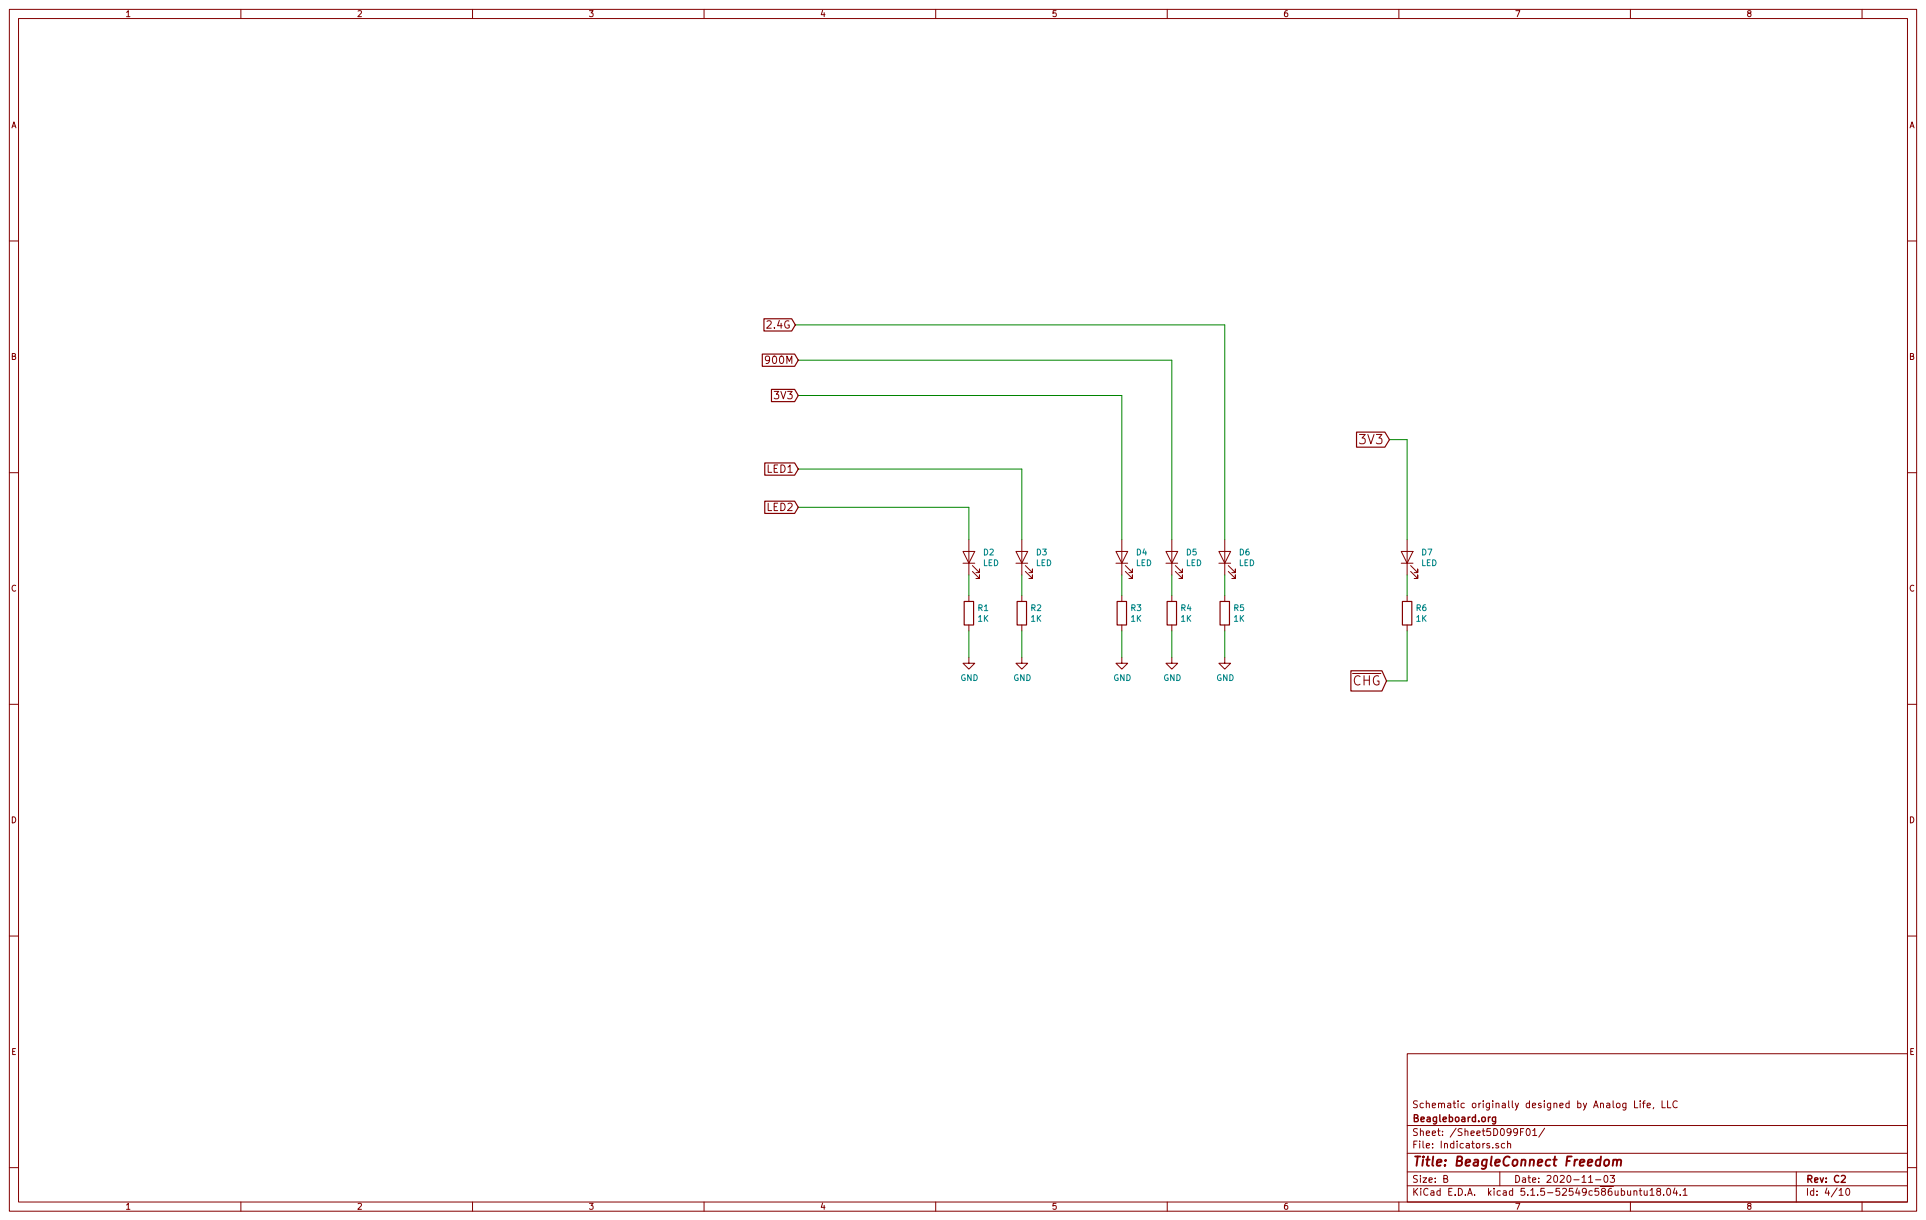
[picture p122: page 4]

File: Indicators.sch Sheet: /Sheet5D099F01/ Beagleboard.org Schematic originally designed by Analog Life, LLC

Id: 4/10 Title: BeagleConnect Freedom

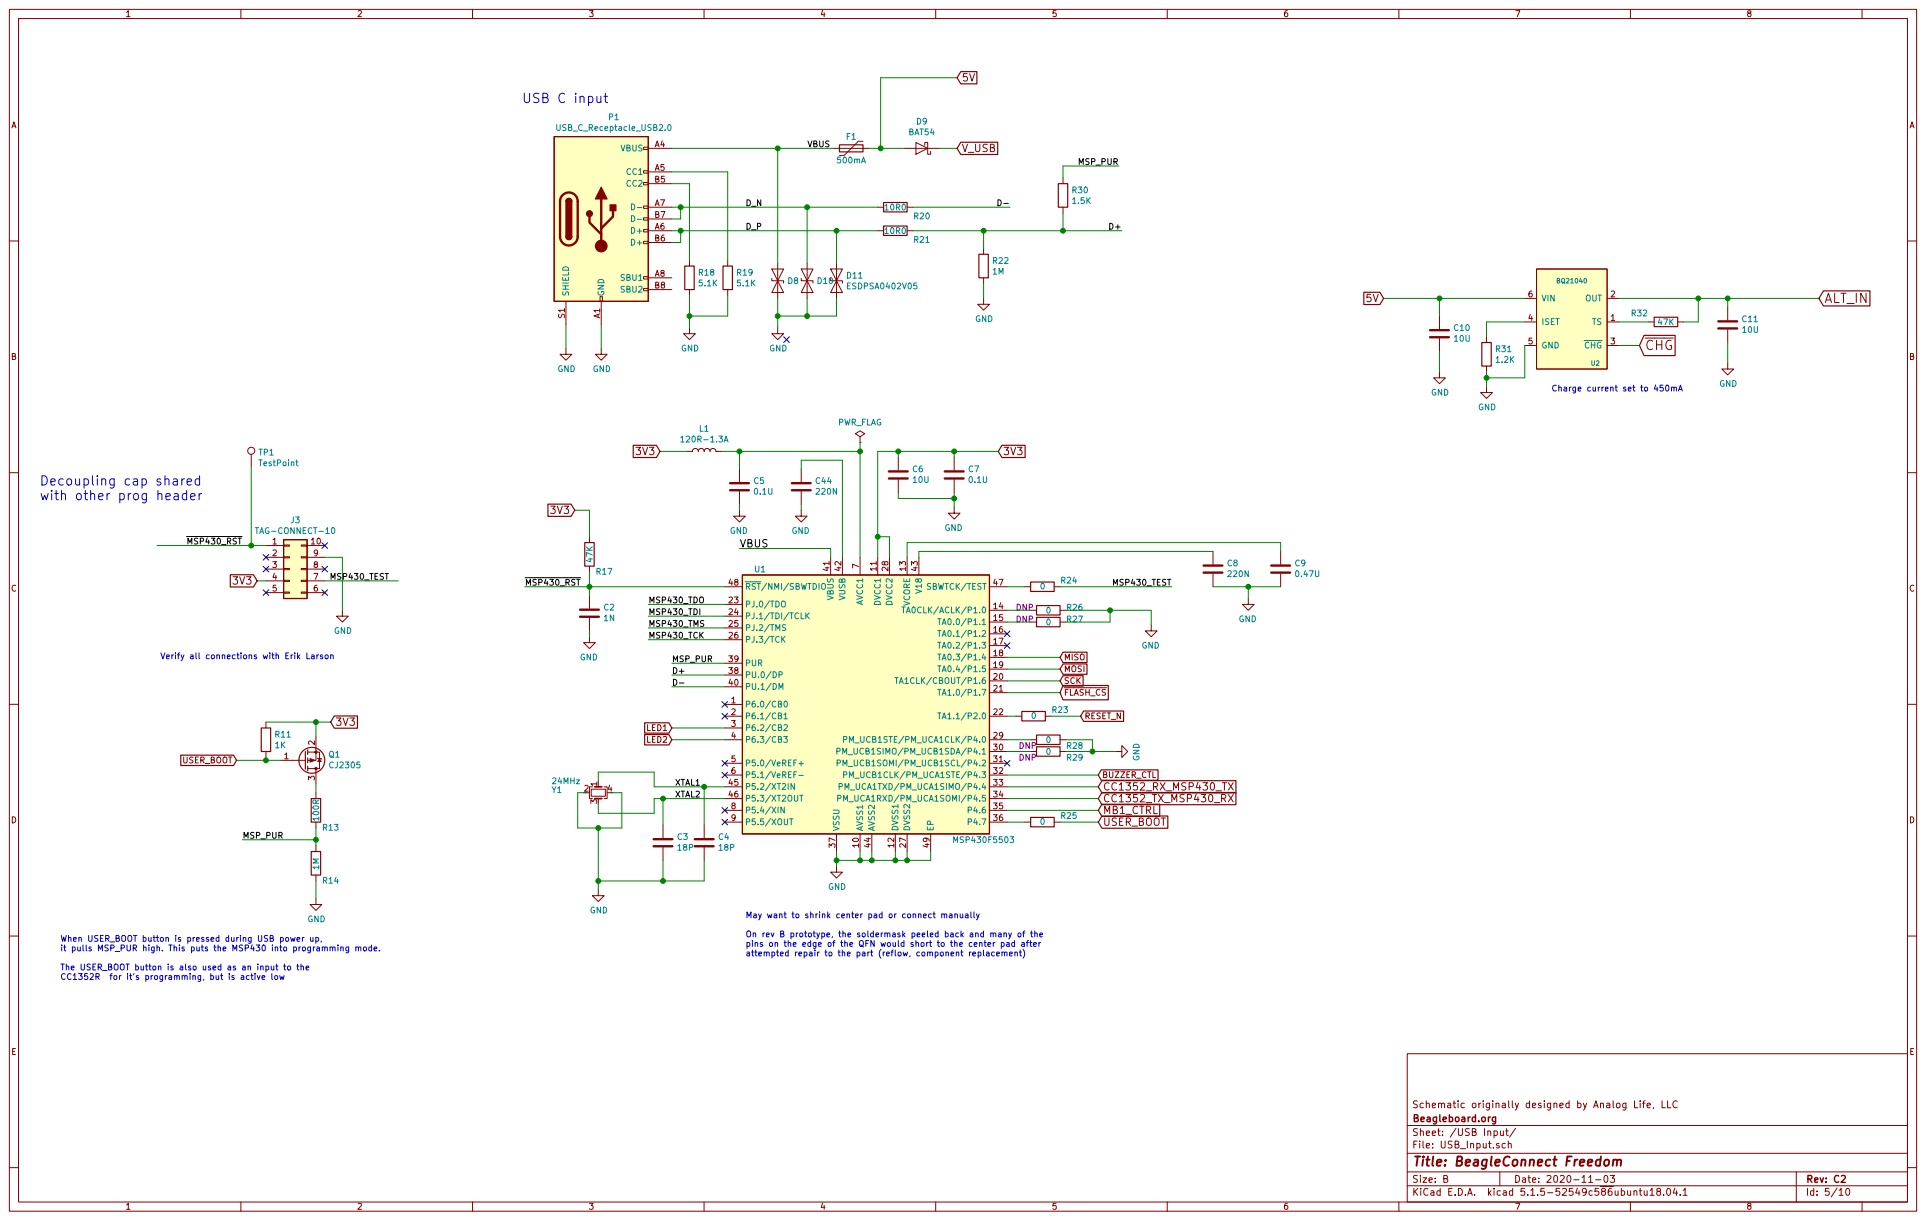
[picture p123: page 5]

Charge current set to 450mA

Verify all connections with Erik Larson Decoupling cap shared
with other prog header When USER_BOOT button is pressed during USB power up,

it pulls MSP_PUR high. This puts the MSP430 into programming mode. The USER_BOOT button is also used as an input to the CC1352R for it's programming, but is active low

File: USB_Input.sch Sheet: /USB Input/ Beagleboard.org Schematic originally designed by Analog Life, LLC

Id: 5/10 Title: BeagleConnect Freedom

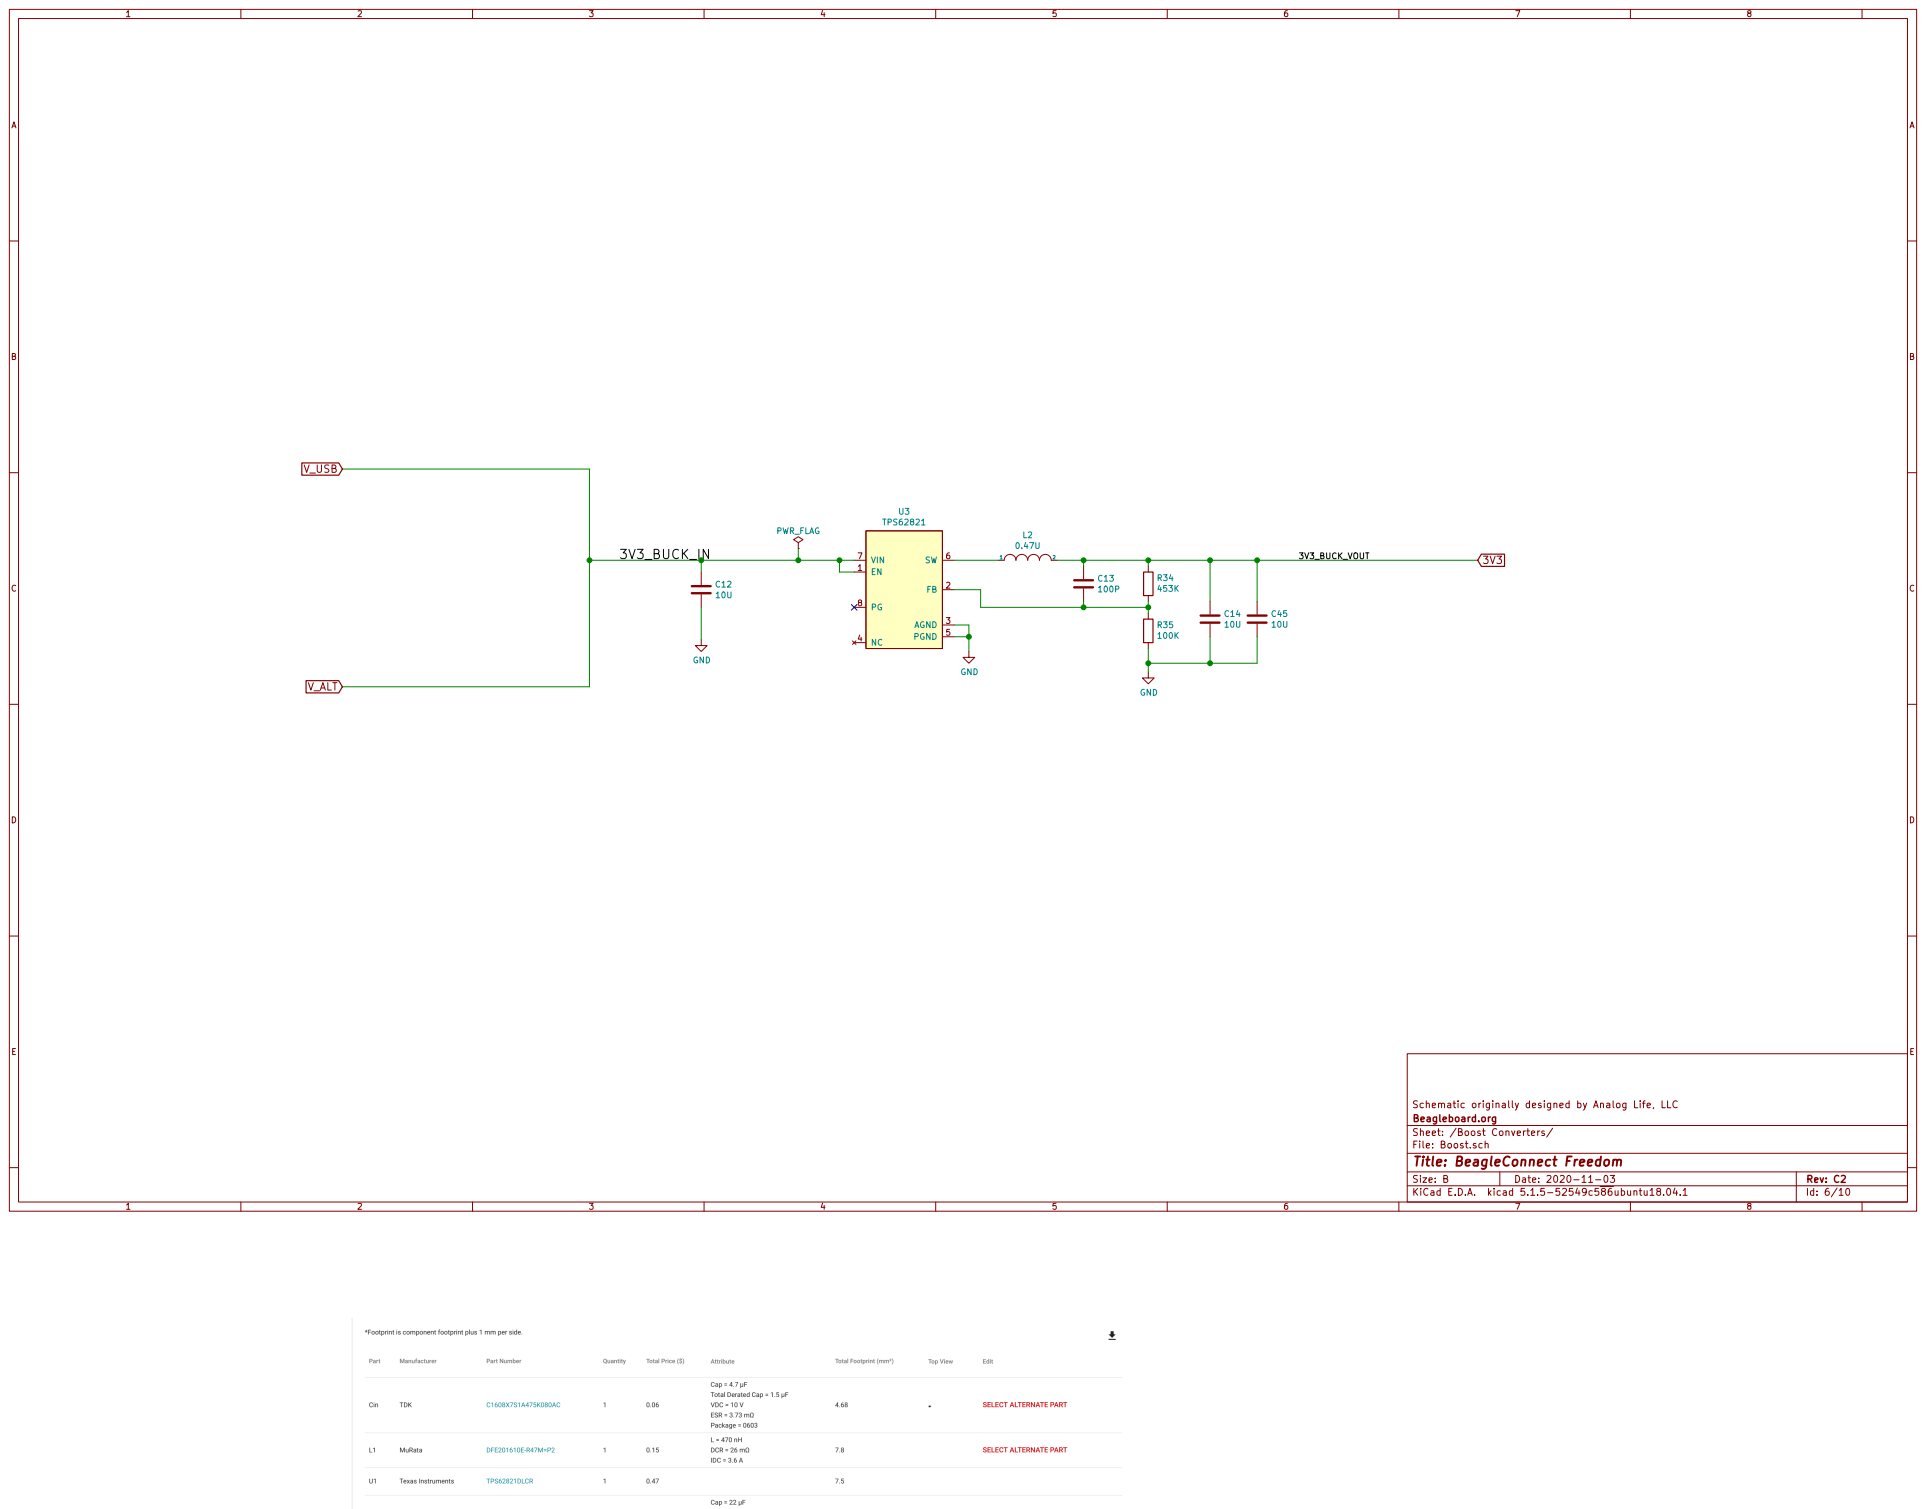
[picture p124: page 6]

File: Boost.sch Sheet: /Boost Converters/ Beagleboard.org Schematic originally designed by Analog Life, LLC

Id: 6/10 Title: BeagleConnect Freedom

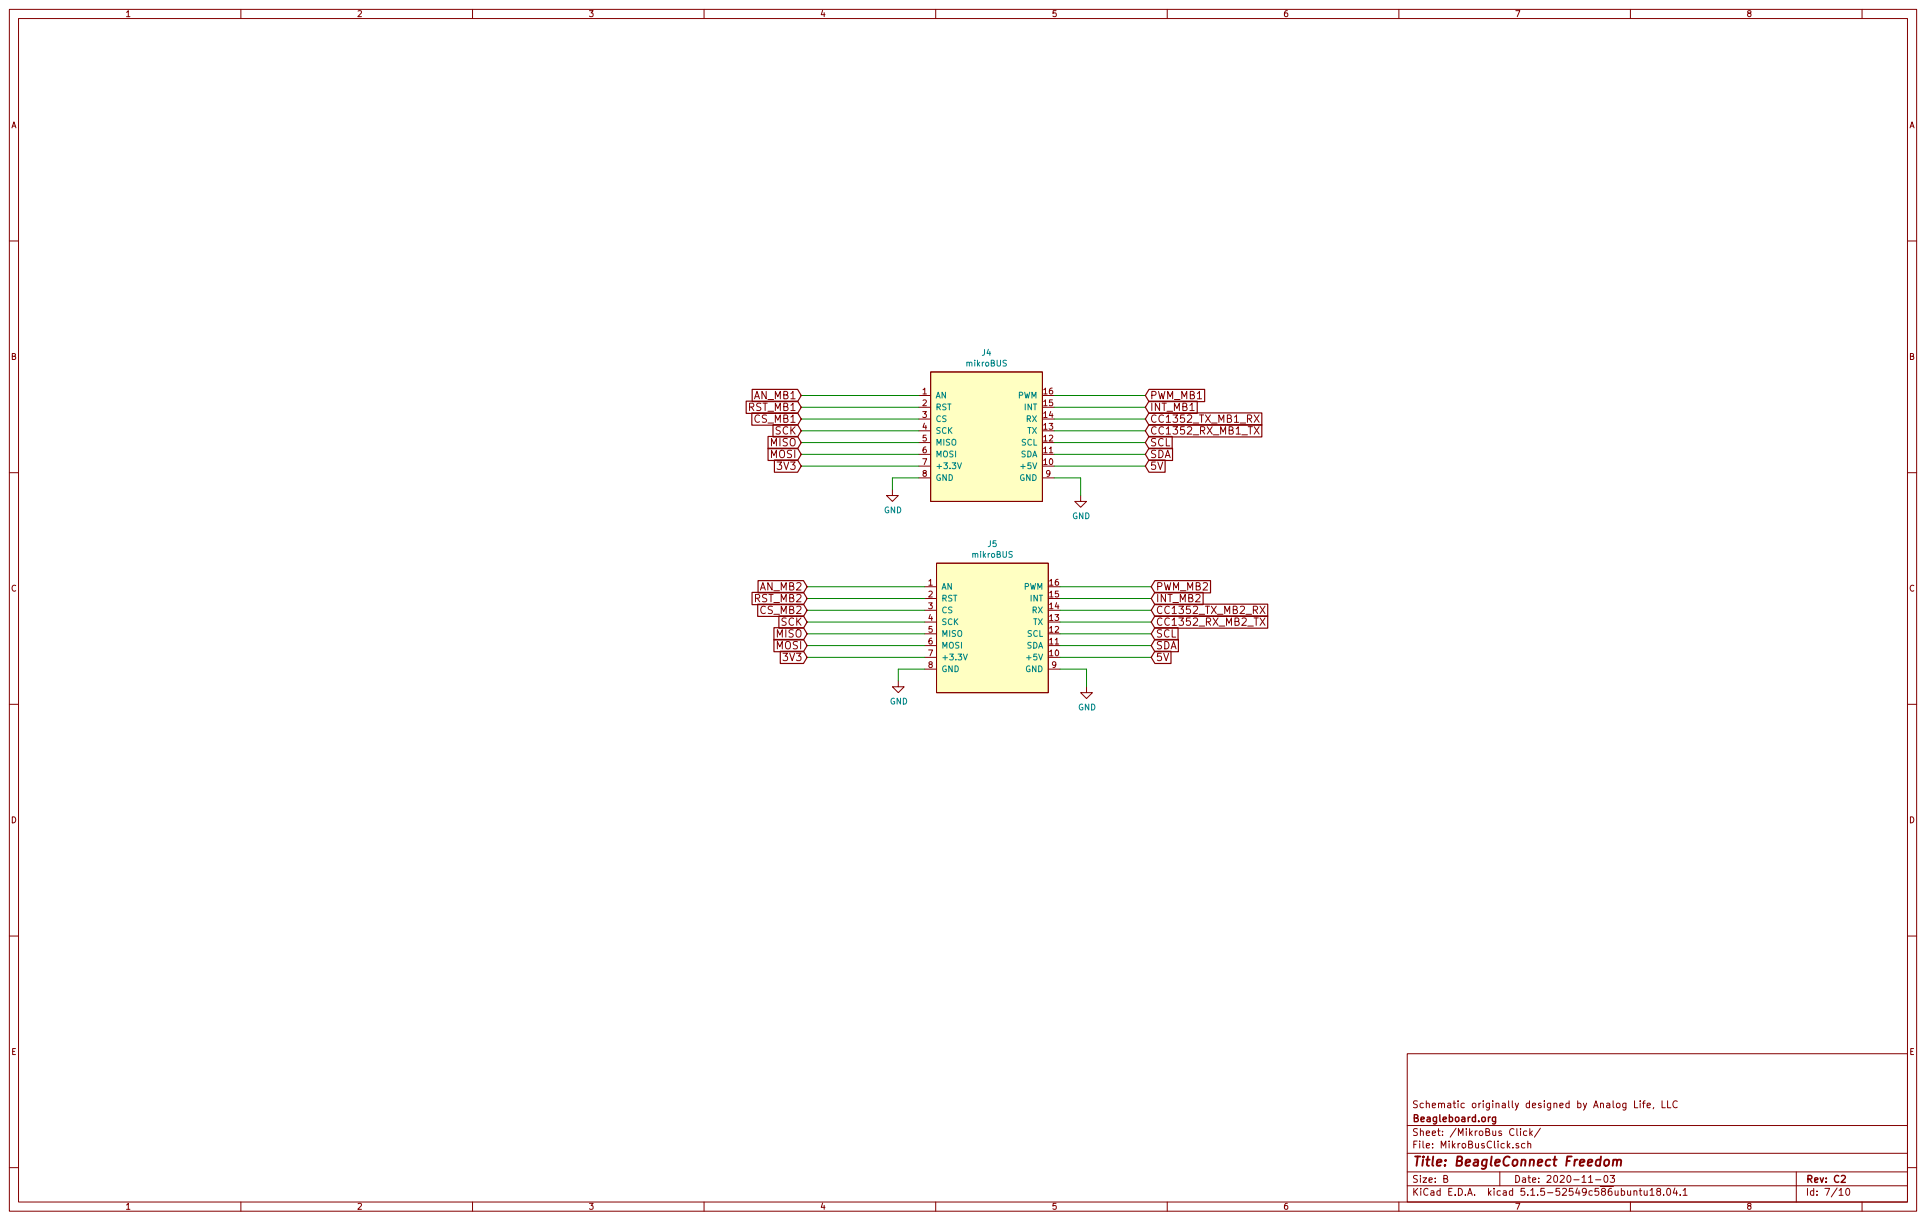
[picture p125: page 7]

SCK CS_MB1 RST_MB1 CS_MB2 RST_MB2
J5 mikroBUS AN_MB2 SCK MISO MOSI 3V3

File: MikroBusClick.sch Sheet: /MikroBus Click/ Beagleboard.org Schematic originally designed by Analog Life, LLC

Id: 7/10 Title: BeagleConnect Freedom

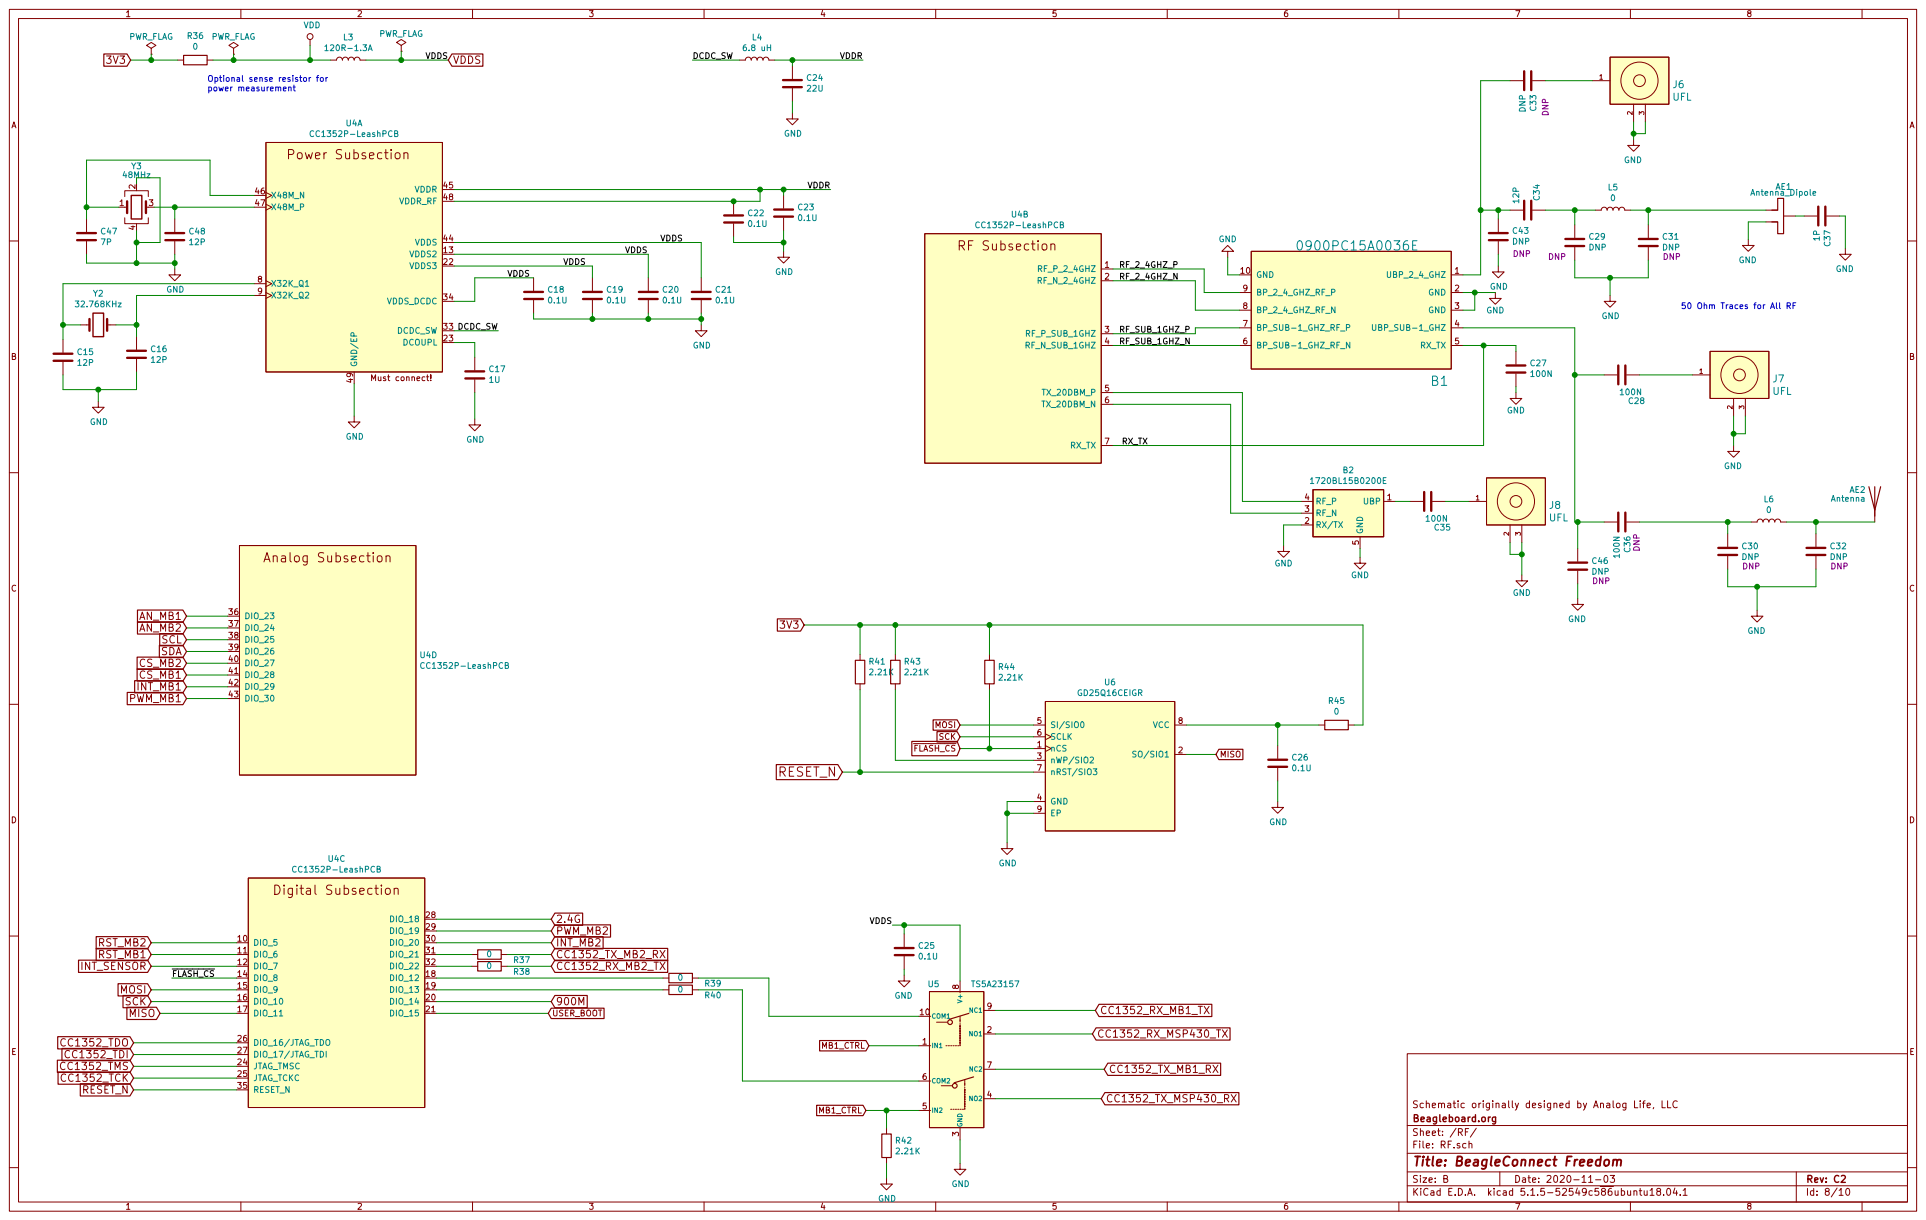
[picture p126: page 8]

3 J7UFL Must connect! Power Subsection

File: RF.sch Sheet: /RF/ Beagleboard.org Schematic originally designed by Analog Life, LLC

Id: 8/10 Title: BeagleConnect Freedom

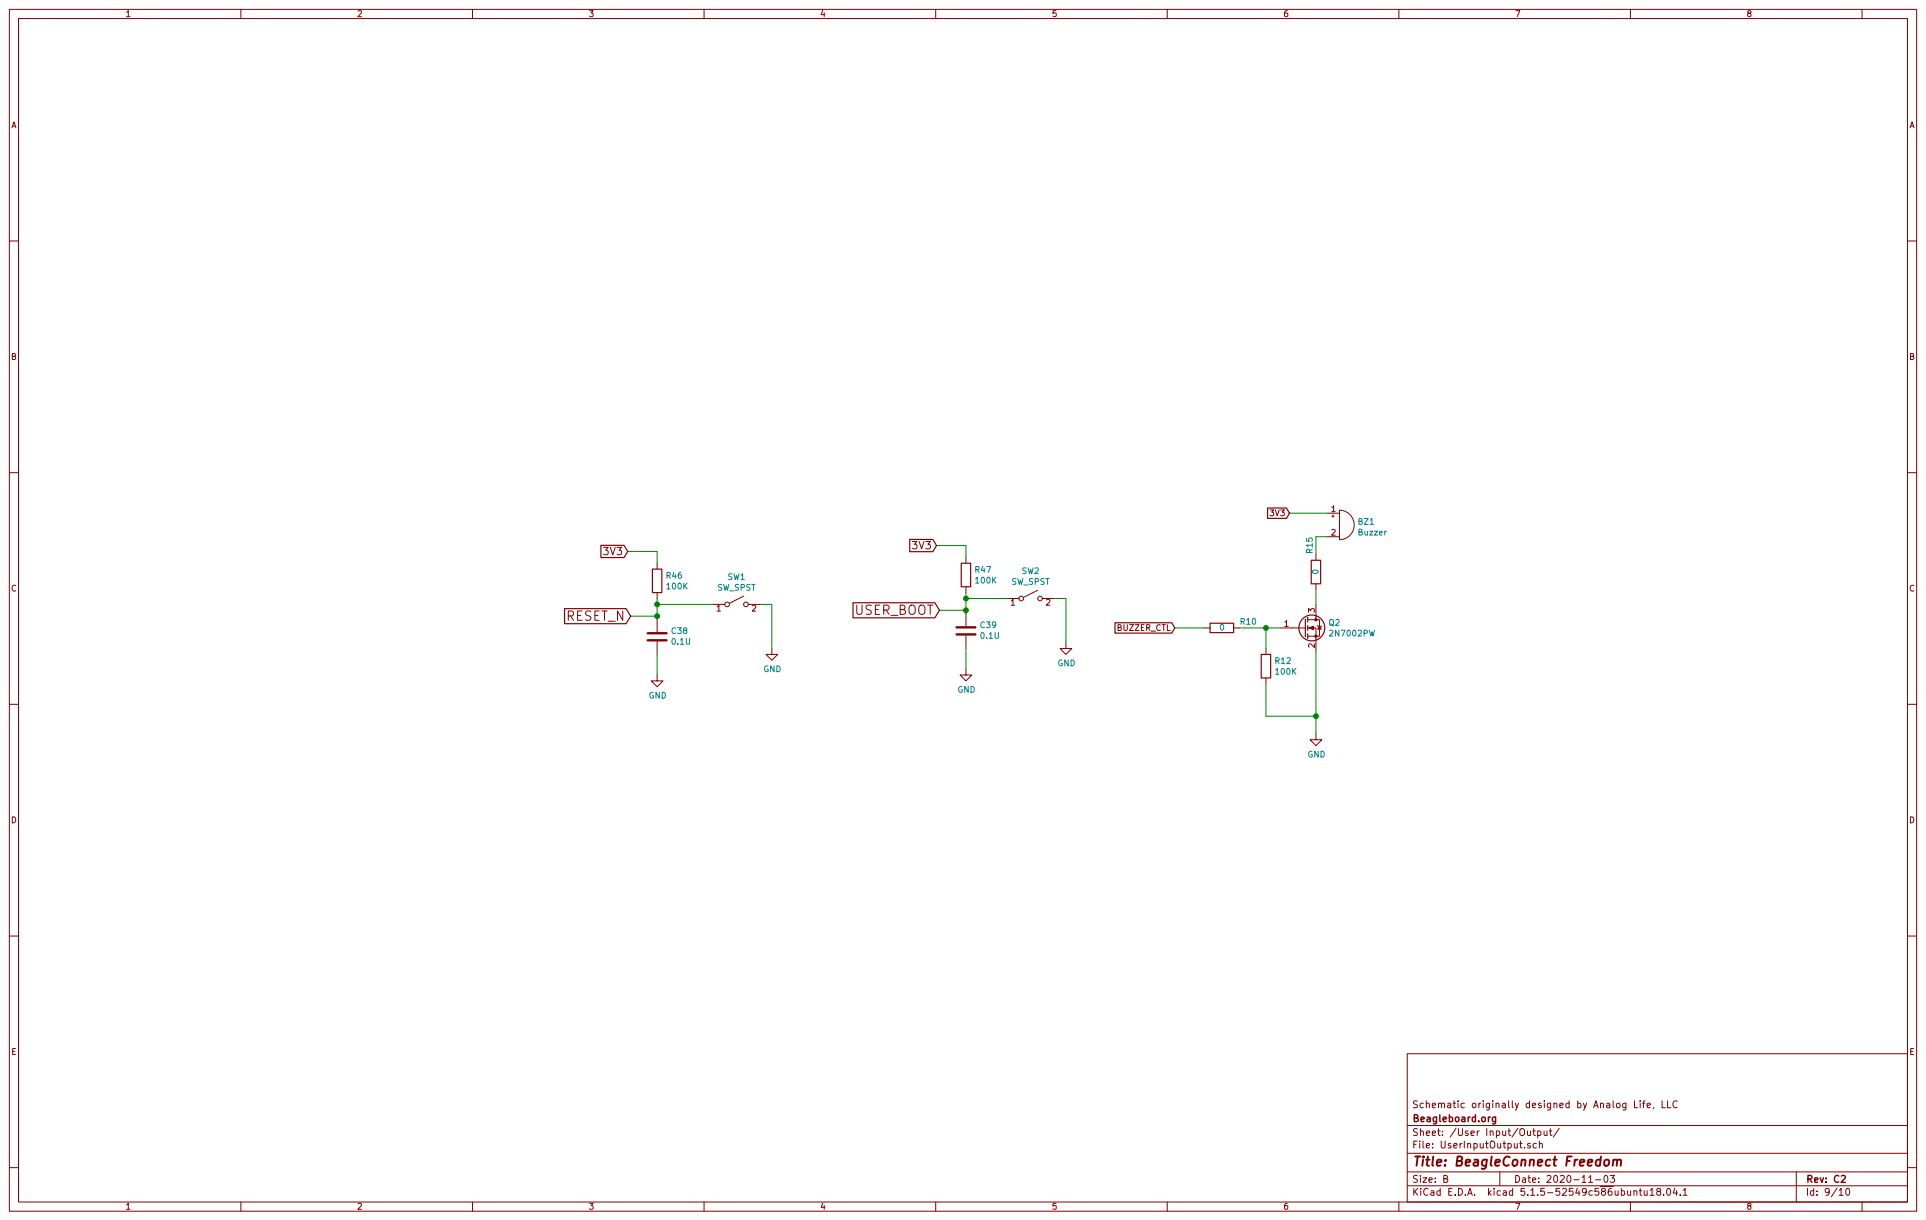
[picture p127: page 9]

File: UserInputOutput.sch Sheet: /User Input/Output/ Beagleboard.org Schematic originally designed by Analog Life, LLC

Id: 9/10 Title: BeagleConnect Freedom

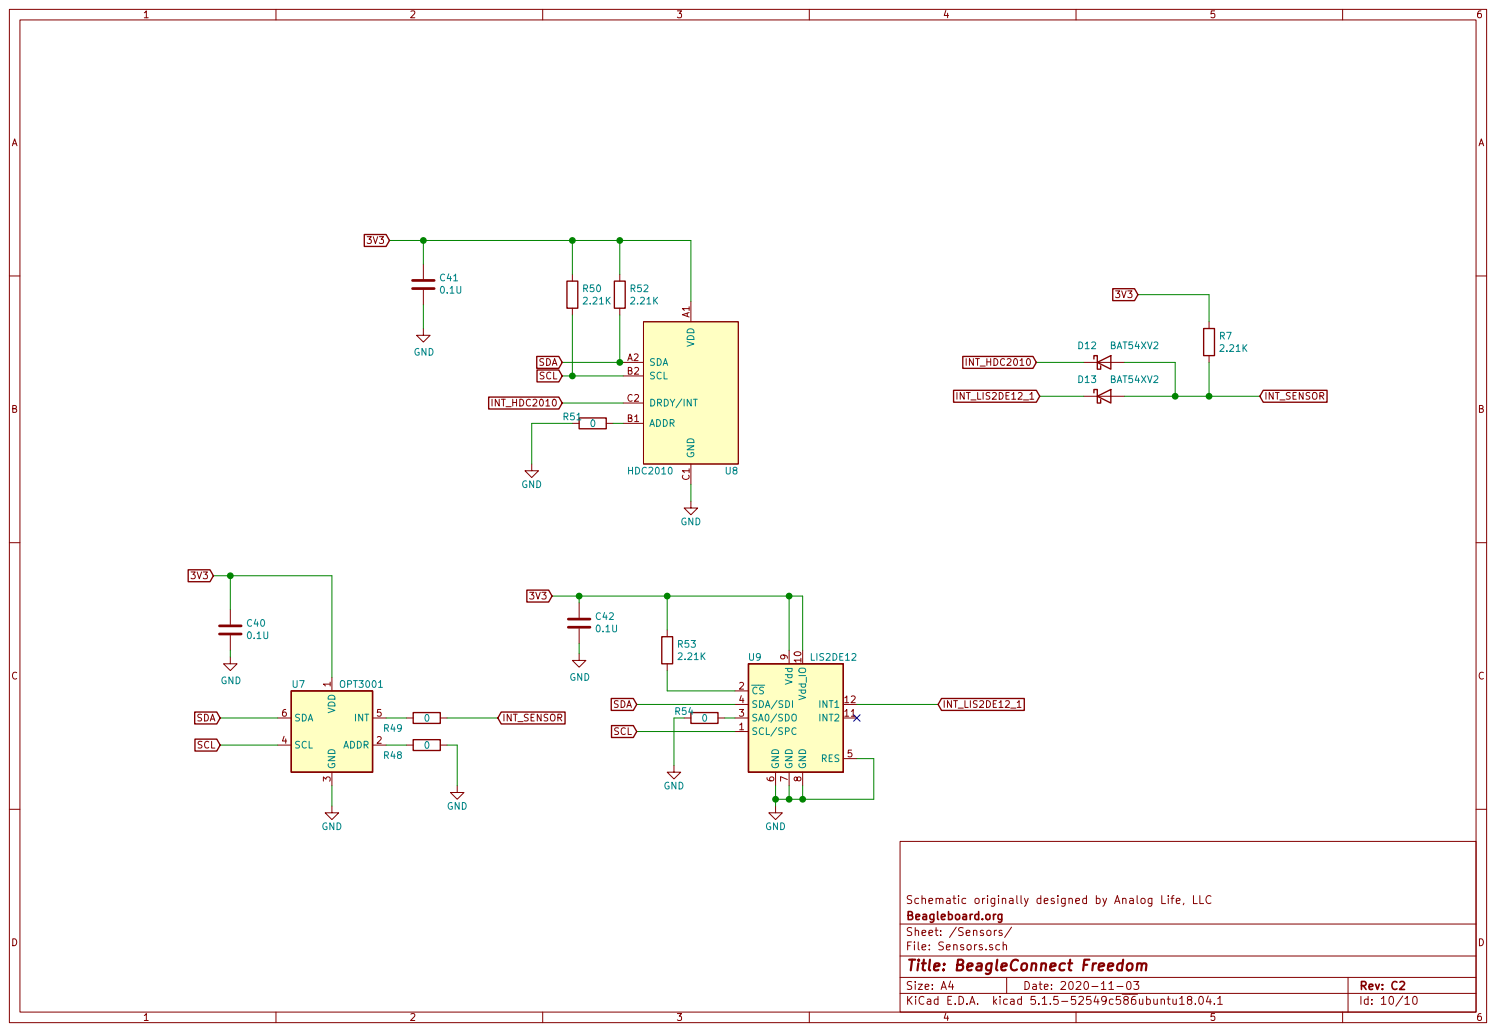
[picture p128: page 10]

Schematic originally designed by Analog Life, LLC
File: Sensors.sch Sheet: /Sensors/ Beagleboard.org

Id: 10/10 Title: BeagleConnect Freedom
